sri299792458/robot-calibration-aprilcube-prototype/artifacts/g1_coupon_r2/renders/compact_coupons.png

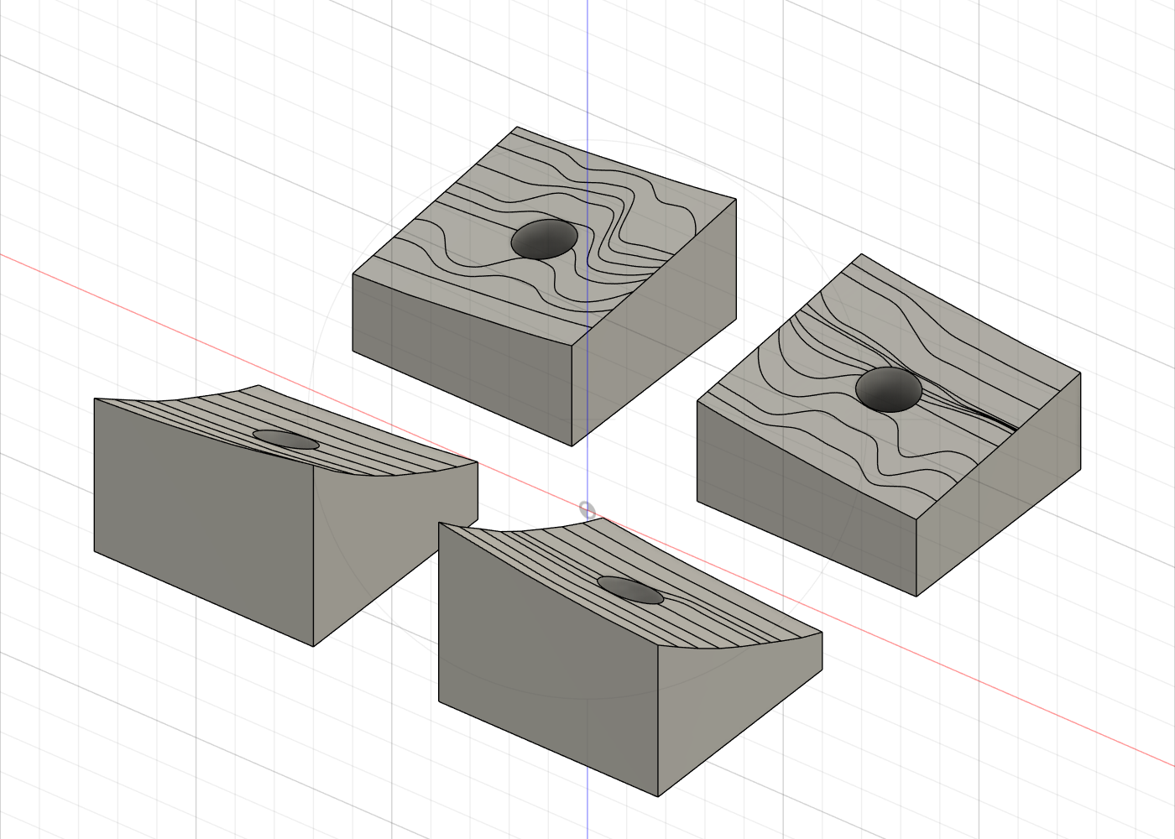
artifacts/g1_coupon_r2/renders/compact_coupons.png
