sri299792458/robot-calibration-aprilcube-prototype/artifacts/g1_coupon_r2/renders/identification_marks.png

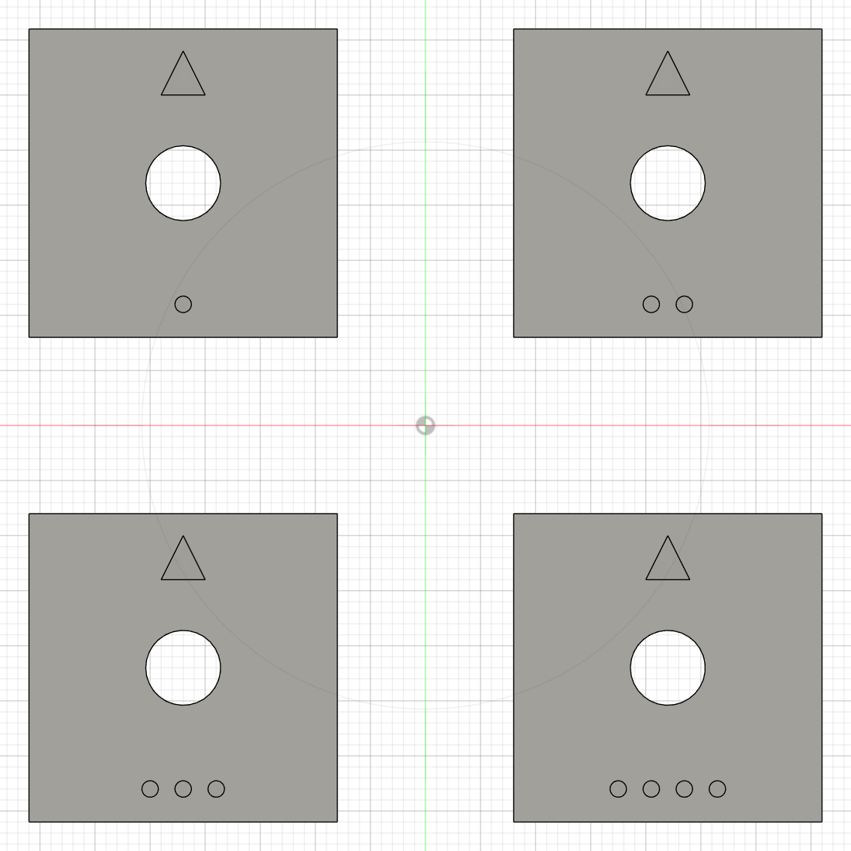
artifacts/g1_coupon_r2/renders/identification_marks.png
