sri299792458/robot-calibration-aprilcube-prototype/artifacts/g1_mount_v7/renders/board_connections.png

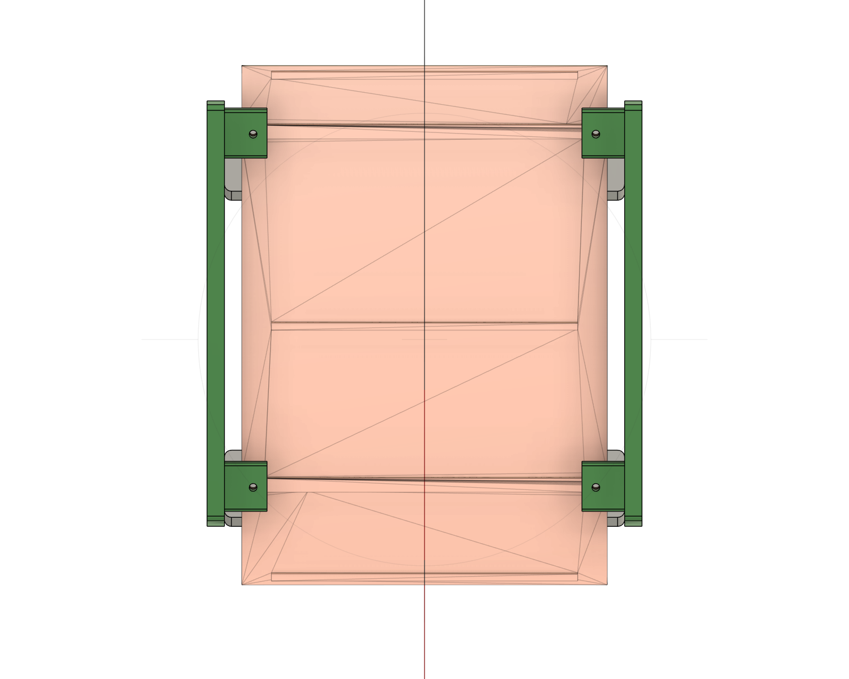
artifacts/g1_mount_v7/renders/board_connections.png
