sri299792458/robot-calibration-aprilcube-prototype/artifacts/g1_mount_v7/renders/m6_root_section.png

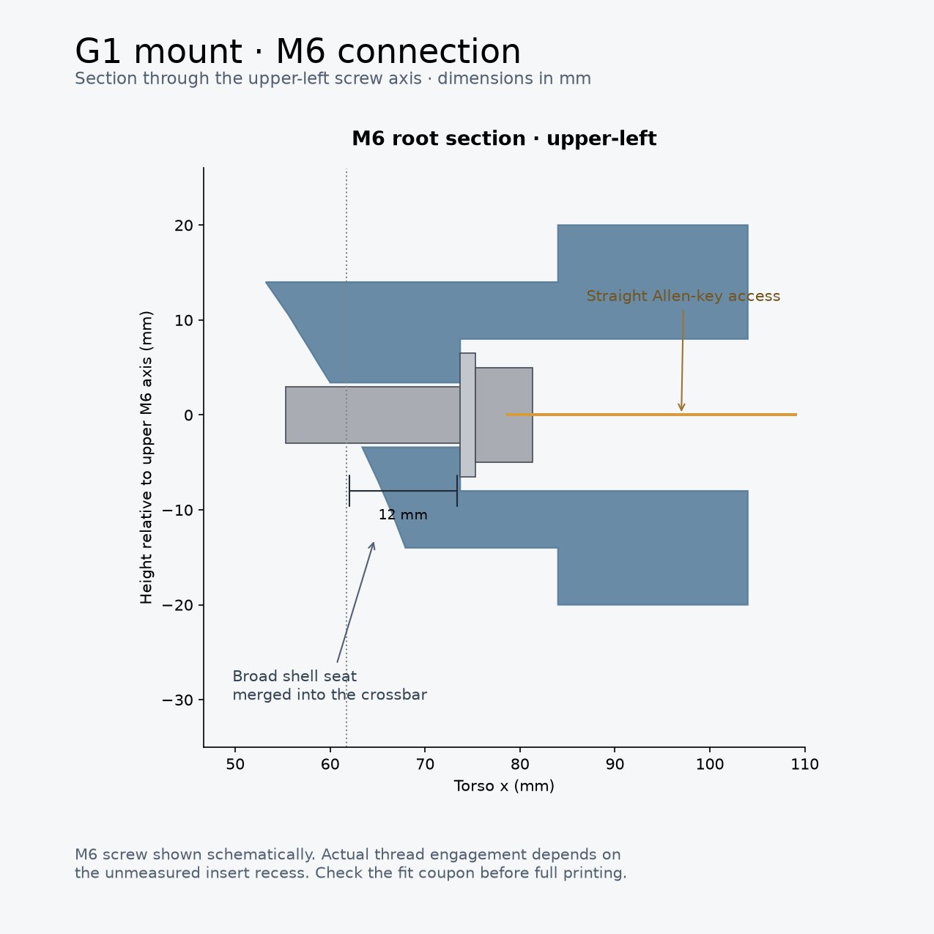
artifacts/g1_mount_v7/renders/m6_root_section.png
