sri299792458/robot-calibration-aprilcube-prototype/renders/dual_dex3_segmented_collision_envelopes.png

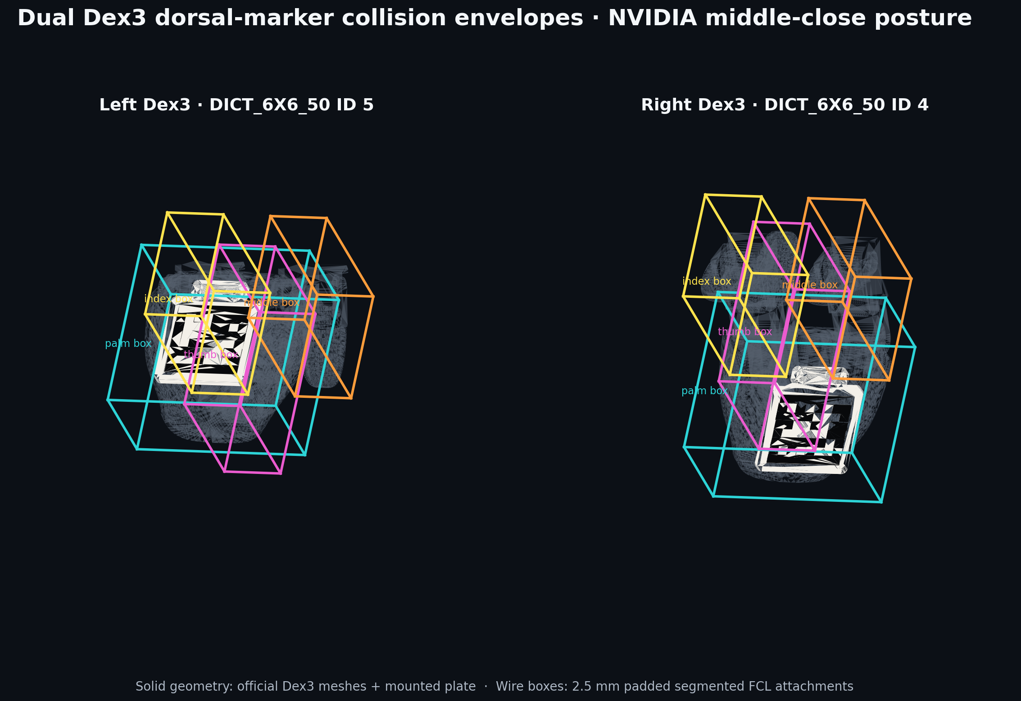
renders/dual_dex3_segmented_collision_envelopes.png
