sri299792458/robot-calibration-aprilcube-prototype/cad/dex3_dorsal_aruco_mount/carrier_white_pla.stl

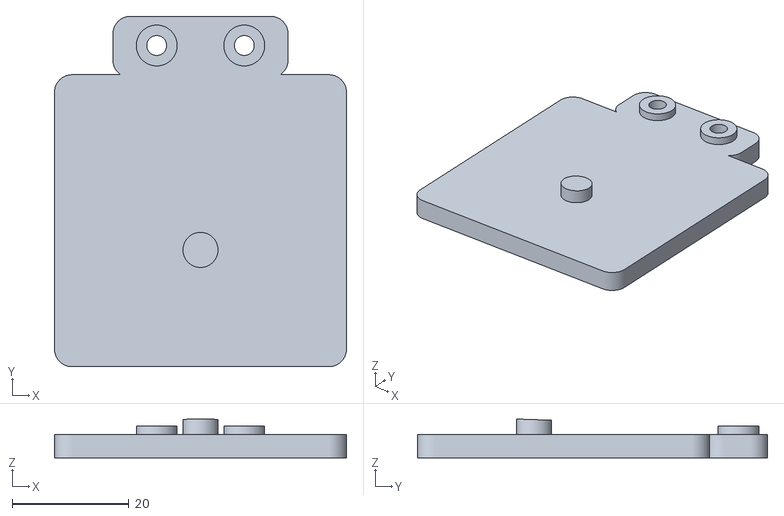
[picture p27: CAD file, 2026-09-21]
cad/dex3_dorsal_aruco_mount/carrier_white_pla.stl
50.0 x 60.0 x 6.67
