sri299792458/robot-calibration-aprilcube-prototype/cad/torso_charuco_fixture/carrier_multicolor_h2d.3mf

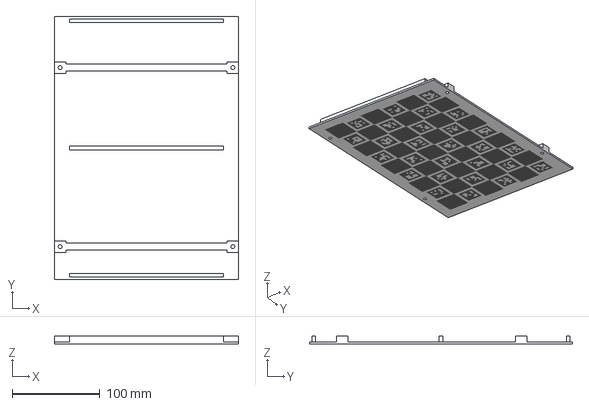
[picture p29: CAD file, 2026-09-21]
cad/torso_charuco_fixture/carrier_multicolor_h2d.3mf
210.0 x 300.0 x 9.40 mm
