sri299792458/robot-calibration-aprilcube-prototype/artifacts/g1_coupon_r2/original_reference/FIT_ONLY_lower_right_PRINT.stl

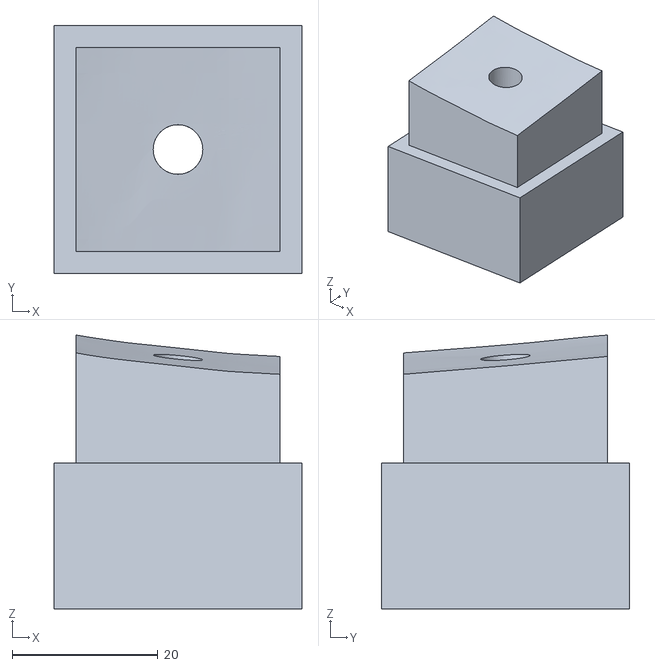
[picture p30: CAD file, 2026-09-21]
artifacts/g1_coupon_r2/original_reference/FIT_ONLY_lower_right_PRINT.stl
34.0 x 34.0 x 37.6
