sri299792458/robot-calibration-aprilcube-prototype/cad/dex3_dorsal_aruco_mount/aruco_black_pla.stl

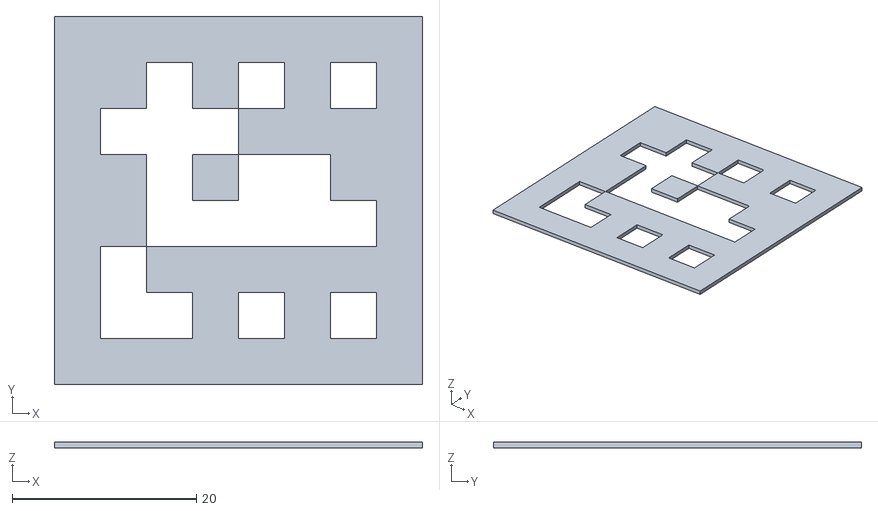
[picture p32: CAD file, 2026-09-21]
cad/dex3_dorsal_aruco_mount/aruco_black_pla.stl
40.0 x 40.0 x 0.6
