sri299792458/robot-calibration-aprilcube-prototype/artifacts/g1_mount_v7/renders/fusion_assembly.png

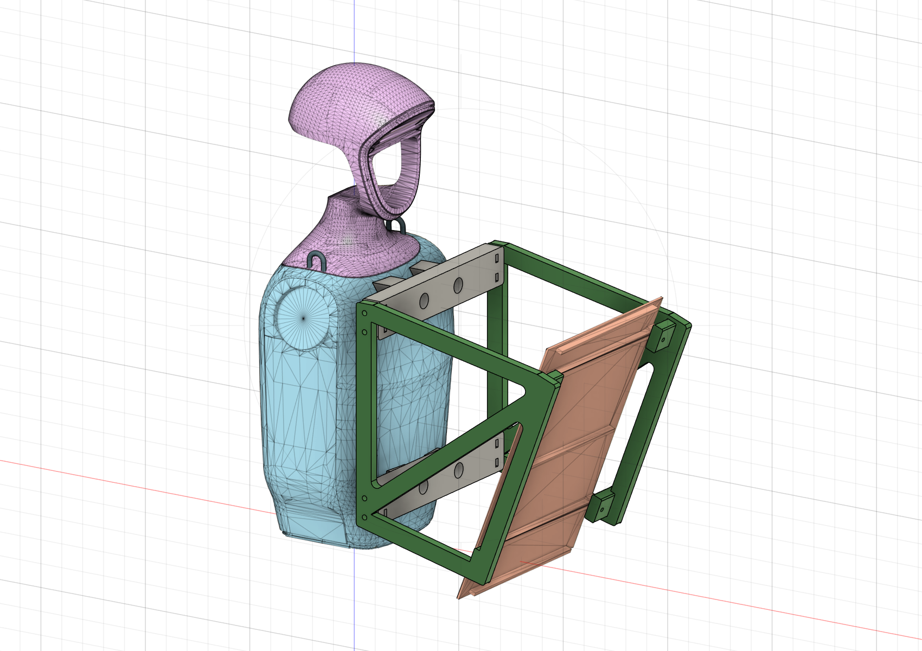
artifacts/g1_mount_v7/renders/fusion_assembly.png
