sri299792458/robot-calibration-aprilcube-prototype/artifacts/g1_mount_v7/renders/print_orientations.png

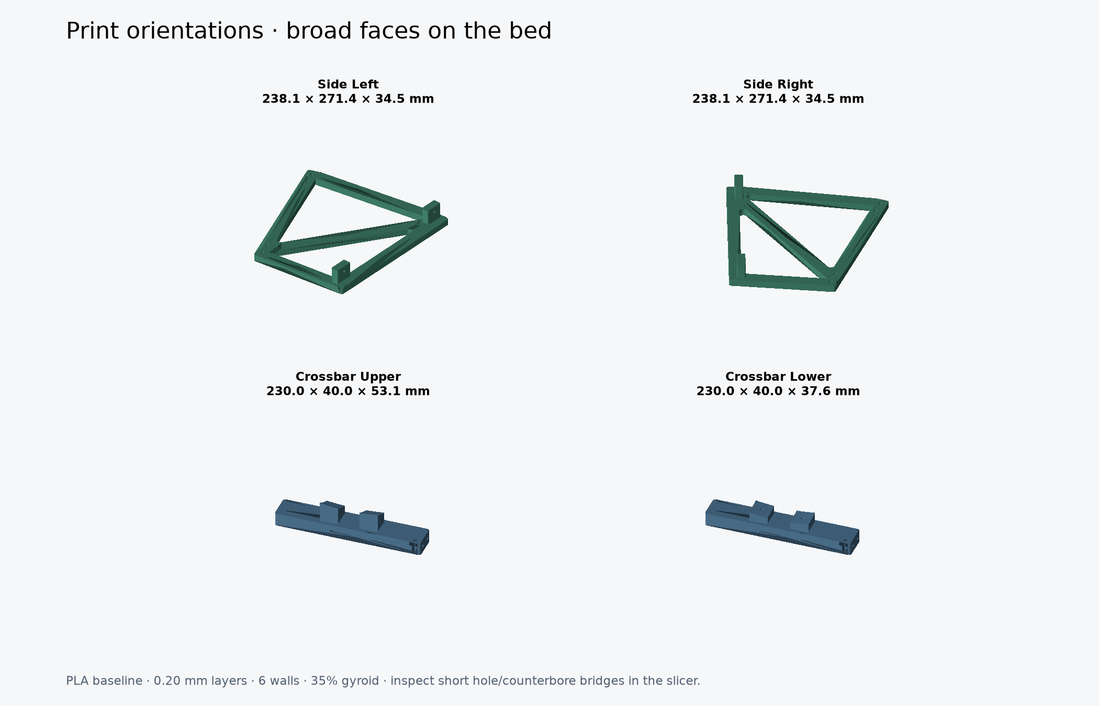
artifacts/g1_mount_v7/renders/print_orientations.png
