sri299792458/robot-calibration-aprilcube-prototype/src/g1_aprilcube_calibration/hardware_cli.py

"""Explicitly armed G1 commissioning and rectified-session collection commands."""

from __future__ import annotations

import argparse
import hashlib
import json
import os
import signal
import sys
import tempfile
import termios
import time
import tty
from collections.abc import Callable
from concurrent.futures import (
    ProcessPoolExecutor,
    as_completed,
)
from concurrent.futures import (
    TimeoutError as FuturesTimeoutError,
)
from dataclasses import replace
from itertools import pairwise
from multiprocessing import get_context
from pathlib import Path

import cv2
import numpy as np
import yaml
from scipy.spatial.transform import Rotation

from aprilcube import CorrespondenceDetector
from g1_aprilcube_calibration.activation_handoff import (
    ActivationHandoff,
    build_activation_handoff,
)
from g1_aprilcube_calibration.authored_collection import (
    AuthoredCollectionPlan,
    exposed_target_normal_from_hardware,
    modeled_hand_T_target_from_hardware,
    validate_exposed_camera_views,
    validate_hardware_target_profile,
    validate_modeled_hand_target_binding,
)
from g1_aprilcube_calibration.camera_models import RectifiedCameraInfo
from g1_aprilcube_calibration.capture_diagnostics import supported_vs_held_metrics
from g1_aprilcube_calibration.clock import SystemClock
from g1_aprilcube_calibration.collision import (
    CollisionConfig,
    FCLCollisionChecker,
)
from g1_aprilcube_calibration.config import QualityThresholds
from g1_aprilcube_calibration.dual_arm_clearance import (
    DUAL_CLEARANCE_POSE_ID,
    RIGHT_CLEARANCE_POSE_ID,
    DualArmClearanceExecutor,
    live_dex3_collision_config,
    plan_dual_arm_shoulder_clearance,
    validate_dex3_finger_sweep_at_state,
)
from g1_aprilcube_calibration.executor_driver import (
    ExecutorControlDriver,
    SynchronizedPoseExecutor,
)
from g1_aprilcube_calibration.executor_state_machine import (
    ExecutorConfig,
    ExecutorState,
    PoseExecutor,
)
from g1_aprilcube_calibration.gravity_compensation import (
    UNITREE_XR_GRAVITY_REFERENCE,
    G1PinocchioGravityFeedforward,
)
from g1_aprilcube_calibration.inverse_kinematics import IKConfig
from g1_aprilcube_calibration.joint_map import (
    G1_29_JOINT_NAMES,
    LEFT_ARM_INDICES,
    RIGHT_ARM_INDICES,
    arm_hand_link,
    arm_joint_names,
    validate_full_joint_vector,
)
from g1_aprilcube_calibration.live_capture import LiveBurstConfig, LiveBurstFrameSource
from g1_aprilcube_calibration.models import utc_now_iso
from g1_aprilcube_calibration.pc2_safety import (
    PC2DampingWatchdog,
    PC2SafetyConfig,
)
from g1_aprilcube_calibration.pose_recorder import (
    PoseRecorder,
    PoseRecordingRequest,
)
from g1_aprilcube_calibration.pose_schema import (
    HANDOFF_POSE_ID,
    PoseSet,
)
from g1_aprilcube_calibration.pose_store import PoseStore, TransientPoseStore
from g1_aprilcube_calibration.pose_validator import (
    DirectedEdgeResult,
    PathValidationConfig,
    PosePathValidator,
    ValidationReport,
)
from g1_aprilcube_calibration.preview import render_operator_preview
from g1_aprilcube_calibration.process_lock import CommandOwnerLock
from g1_aprilcube_calibration.quality import (
    CameraIntrinsics,
    PoseQualityEvaluator,
    QualityGrade,
    ViewSignature,
)
from g1_aprilcube_calibration.readiness import RecordingGateConfig, StateSampleBuffer
from g1_aprilcube_calibration.ros.camera_adapter import (
    ROSCameraSubscriber,
    ROSImageFrame,
)
from g1_aprilcube_calibration.session_runner import (
    ApprovedSessionOrchestrator,
    AuthoredCollectionOrchestrator,
    CaptureSessionRunner,
    SessionExecutionPlan,
)
from g1_aprilcube_calibration.session_runtime_log import SessionRuntimeLog
from g1_aprilcube_calibration.session_store import IsolatedSessionStore, SessionStore
from g1_aprilcube_calibration.table_accuracy import (
    CharucoBoardPoseDetector,
    CharucoBoardSpec,
    create_evaluation_document,
    create_plan_document,
    hand_target_from_board,
    load_plan_document,
    observe_burst,
    predicted_board_T_cube_from_model,
)
from g1_aprilcube_calibration.table_motion import (
    TABLE_ESCAPE_POSE_ID,
    TABLE_TARGET_POSE_ID,
    TablePlaneConfig,
    build_lifted_start_cube_target,
    build_table_motion_preflight,
    validate_table_plane_escape_path,
    validate_table_plane_path,
)
from g1_aprilcube_calibration.teaching_controller import (
    TeachingArmController,
    TeachingConfig,
    TeachingState,
)
from g1_aprilcube_calibration.teaching_driver import (
    SynchronizedTeachingController,
    TeachingControlDriver,
)
from g1_aprilcube_calibration.timestamp_pairing import PairingConfig
from g1_aprilcube_calibration.transforms import validate_transform
from g1_aprilcube_calibration.transports.base import ArmCommand
from g1_aprilcube_calibration.transports.unitree_arm_sdk import (
    UnitreeArmSDKTransport,
    UnitreeLowStateObserver,
    UnitreeTransportConfig,
)
from g1_aprilcube_calibration.transports.unitree_debug_lowcmd import (
    UnitreeDebugLowCmdConfig,
    UnitreeDebugLowCmdTransport,
)
from g1_aprilcube_calibration.transports.unitree_dex3 import (
    DEX3_CALIBRATION_POSTURE_SOURCE,
    DEX3_MOTOR_JOINT_SUFFIXES,
    Dex3ControlConfig,
    UnitreeDex3PostureController,
    UnitreeDex3StateObserver,
    dex3_motor_joint_name,
)
from g1_aprilcube_calibration.urdf_model import URDFModel

WRITE_ACK = "I UNDERSTAND THIS WRITES RT/ARM_SDK"
DAMP_ACK = "DAMP THE LOAD-BEARING-HARNESSED G1 NOW"
MOTION_ACK = (
    "I CONFIRM THE G1 IS SECURED BY THE LOAD-BEARING HARNESS AND THE WORKSPACE IS CLEAR"
)
LIVE_TEACHING_YELLOW_REASON = "operator accepted yellow warning in live teaching UI"
_MAX_RUNTIME_VALIDATION_WORKERS = 8
_MINIMUM_PARALLEL_VALIDATION_EDGES = 8
_runtime_validation_worker: tuple[PosePathValidator, object, np.ndarray] | None = None
REPLAY_YELLOW_REASON = "yellow visual warning accepted by replay default"


def add_hardware_subparsers(
    subparsers: argparse._SubParsersAction,
    *,
    workspace_root: Path,
    default_target: Path,
    default_quality: Path,
) -> None:
    default_hardware = workspace_root / "config" / "hardware_dex3_aruco.yaml"
    default_collision = workspace_root / "config" / "collision_pairs_dex3_aruco.yaml"
    default_lock = Path("/tmp/g1-aprilcube-calibration-command.lock")

    table_images = subparsers.add_parser(
        "capture-table-images",
        help="save a camera-only lossless burst for the tabletop accuracy test",
    )
    _add_network_arguments(table_images)
    _add_camera_arguments(table_images)
    table_images.add_argument("--output-directory", type=Path, required=True)
    table_images.add_argument("--frame-count", type=int, default=7)
    table_images.add_argument("--camera-timeout-s", type=float, default=10.0)
    table_images.add_argument("--maximum-duration-s", type=float, default=2.0)
    table_images.set_defaults(handler=run_capture_table_images)

    table_execute = subparsers.add_parser(
        "execute-table-accuracy",
        help=(
            "solve a supported-start escape and table target, capture, reverse "
            "to the supported start, restore seated control, and score accuracy"
        ),
    )
    _add_network_arguments(table_execute)
    _add_motion_safety_arguments(table_execute)
    _add_camera_arguments(table_execute)
    table_execute.add_argument("--plan", type=Path, required=True)
    table_execute.add_argument("--output-directory", type=Path, required=True)
    table_execute.add_argument("--hardware-config", type=Path, default=default_hardware)
    table_execute.add_argument(
        "--collision-config", type=Path, default=default_collision
    )
    table_execute.add_argument("--frame-count", type=int, default=7)
    table_execute.add_argument("--camera-timeout-s", type=float, default=10.0)
    table_execute.add_argument("--maximum-burst-duration-s", type=float, default=2.0)
    table_execute.add_argument("--ik-restarts", type=int, default=24)
    table_execute.add_argument("--minimum-board-clearance-mm", type=float, default=10.0)
    table_execute.add_argument("--maximum-board-shift-mm", type=float, default=5.0)
    table_execute.add_argument("--maximum-board-shift-deg", type=float, default=1.0)
    table_execute.add_argument(
        "--confirm", required=True, help=f"must equal: {MOTION_ACK}"
    )
    table_execute.add_argument("--lock-file", type=Path, default=default_lock)
    table_execute.set_defaults(handler=run_execute_table_accuracy)

    zero = subparsers.add_parser(
        "commission-weight-zero",
        help="publish one measured arm target with blend weight zero",
    )
    _add_network_arguments(zero)
    zero.add_argument("--confirm", required=True, help=f"must equal: {WRITE_ACK}")
    zero.add_argument("--timeout-s", type=float, default=5.0)
    zero.add_argument("--lock-file", type=Path, default=default_lock)
    zero.set_defaults(handler=run_commission_weight_zero)

    damping = subparsers.add_parser(
        "commission-damping",
        help="physically verify the PC2 heartbeat watchdog and G1 Damp RPC",
    )
    _add_network_arguments(damping)
    _add_motion_safety_arguments(damping)
    damping.add_argument("--hardware-config", type=Path, default=default_hardware)
    damping.add_argument(
        "--trigger",
        choices=("heartbeat-timeout", "explicit"),
        default="heartbeat-timeout",
    )
    damping.add_argument("--confirm", required=True, help=f"must equal: {DAMP_ACK}")
    damping.set_defaults(handler=run_commission_damping)

    dex3_posture = subparsers.add_parser(
        "commission-dex3-middle-close",
        help=(
            "derive and execute a live collision-validated shoulder-clearance "
            "route, verify NVIDIA middle-close, restore the original fingers "
            "and shoulders, and send terminal Dex3 timeout"
        ),
    )
    _add_network_arguments(dex3_posture)
    _add_motion_safety_arguments(dex3_posture)
    dex3_posture.add_argument("--hardware-config", type=Path, default=default_hardware)
    dex3_posture.add_argument(
        "--collision-config", type=Path, default=default_collision
    )
    dex3_posture.add_argument("--duration-s", type=float, default=2.0)
    dex3_posture.add_argument(
        "--confirm", required=True, help=f"must equal: {MOTION_ACK}"
    )
    dex3_posture.add_argument("--lock-file", type=Path, default=default_lock)
    dex3_posture.set_defaults(handler=run_commission_dex3_middle_close)

    seated_debug_hold = subparsers.add_parser(
        "commission-seated-debug-hold",
        help=(
            "commission zero-displacement seated debug lowcmd takeover and "
            "verified normal FSM 0 -> 1 -> 3 restoration"
        ),
    )
    _add_network_arguments(seated_debug_hold)
    _add_motion_safety_arguments(seated_debug_hold)
    seated_debug_hold.add_argument(
        "--hardware-config", type=Path, default=default_hardware
    )
    seated_debug_hold.add_argument(
        "--collision-config", type=Path, default=default_collision
    )
    seated_debug_hold.add_argument("--duration-s", type=float, default=2.0)
    seated_debug_hold.add_argument(
        "--trigger",
        choices=("restore-seated", "heartbeat-zero-torque"),
        default="restore-seated",
        help=(
            "restore AI through verified FSM 0 -> 1 -> 3 or "
            "deliberately stop command/heartbeat publication and verify PC2 "
            "independently restores AI in zero-torque FSM 0"
        ),
    )
    seated_debug_hold.add_argument(
        "--confirm", required=True, help=f"must equal: {MOTION_ACK}"
    )
    seated_debug_hold.add_argument("--lock-file", type=Path, default=default_lock)
    seated_debug_hold.set_defaults(handler=run_commission_seated_debug_hold)

    teach = subparsers.add_parser(
        "teach-poses",
        help=(
            "continuously guide the arm through arm_sdk, freeze measured poses, "
            "and record paired supported/held calibration bursts"
        ),
    )
    _add_network_arguments(teach)
    _add_motion_safety_arguments(teach)
    teach.add_argument("--session-directory", type=Path, required=True)
    teach.add_argument("--session-id", required=True)
    _add_camera_arguments(teach)
    teach.add_argument("--hardware-config", type=Path, default=default_hardware)
    teach.add_argument("--collision-config", type=Path, default=default_collision)
    teach.add_argument("--target-config", type=Path, default=default_target)
    teach.add_argument("--quality-config", type=Path, default=default_quality)
    teach.add_argument("--camera-timeout-s", type=float, default=10.0)
    teach.add_argument("--guide-camera-timeout-s", type=float, default=1.0)
    teach.add_argument("--burst-timeout-s", type=float, default=15.0)
    teach.add_argument("--group", default="calibration")
    teach.add_argument("--first-pose-id", default="pose_001")
    teach.add_argument("--preview-directory", type=Path)
    teach.add_argument(
        "--yellow-override-reason",
        help=(
            "optional custom note for yellow views; without it, SPACE accepts yellow "
            "and stores the standard live-operator warning"
        ),
    )
    teach.add_argument("--confirm", required=True, help=f"must equal: {MOTION_ACK}")
    teach.add_argument("--lock-file", type=Path, default=default_lock)
    teach.set_defaults(handler=run_teach_poses)

    hold = subparsers.add_parser(
        "commission-hold",
        help="derive a stationary handoff, then acquire/release arm_sdk there",
    )
    _add_network_arguments(hold)
    _add_motion_safety_arguments(hold)
    hold.add_argument("--pose-set", type=Path, required=True)
    hold.add_argument("--hardware-config", type=Path, default=default_hardware)
    hold.add_argument("--collision-config", type=Path, default=default_collision)
    hold.add_argument("--duration-s", type=float, default=2.0)
    hold.add_argument("--confirm", required=True, help=f"must equal: {MOTION_ACK}")
    hold.add_argument("--lock-file", type=Path, default=default_lock)
    hold.set_defaults(handler=run_commission_hold)

    pose = subparsers.add_parser(
        "commission-pose",
        help="validate a live handoff, visit one pose, return, and release",
    )
    _add_network_arguments(pose)
    _add_motion_safety_arguments(pose)
    pose.add_argument("--pose-set", type=Path, required=True)
    pose.add_argument("--validation-report", type=Path, required=True)
    pose.add_argument("--target-pose", required=True)
    pose.add_argument("--hardware-config", type=Path, default=default_hardware)
    pose.add_argument("--collision-config", type=Path, default=default_collision)
    pose.add_argument("--confirm", required=True, help=f"must equal: {MOTION_ACK}")
    pose.add_argument("--lock-file", type=Path, default=default_lock)
    pose.set_defaults(handler=run_commission_pose)

    collect = subparsers.add_parser(
        "collect-session",
        help="execute a passed pose plan and write an immutable rectified session",
    )
    _add_network_arguments(collect)
    _add_motion_safety_arguments(collect)
    collect.add_argument("--pose-set", type=Path, required=True)
    collect.add_argument("--validation-report", type=Path, required=True)
    collect.add_argument("--plan-yaml", type=Path, required=True)
    collect.add_argument("--session-directory", type=Path, required=True)
    collect.add_argument("--session-id", required=True)
    _add_camera_arguments(collect)
    collect.add_argument("--hardware-config", type=Path, default=default_hardware)
    collect.add_argument("--collision-config", type=Path, default=default_collision)
    collect.add_argument("--target-config", type=Path, default=default_target)
    collect.add_argument("--quality-config", type=Path, default=default_quality)
    collect.add_argument("--camera-timeout-s", type=float, default=10.0)
    collect.add_argument("--burst-timeout-s", type=float, default=3.0)
    collect.add_argument(
        "--head-witness-ack",
        action="store_true",
        required=True,
        help="confirm the current fixed camera/head witness mark before collection",
    )
    collect.add_argument("--auto-confirm-transitions", action="store_true")
    collect.add_argument("--no-window", action="store_true")
    collect.add_argument("--confirm", required=True, help=f"must equal: {MOTION_ACK}")
    collect.add_argument("--lock-file", type=Path, default=default_lock)
    collect.set_defaults(handler=run_collect_session)

    collect_auto = subparsers.add_parser(
        "collect-auto",
        help=(
            "execute an authored standing calibration route, automatically "
            "capture valid views, and skip red/invisible targets"
        ),
    )
    _add_network_arguments(collect_auto)
    _add_motion_safety_arguments(collect_auto)
    collect_auto.add_argument("--plan", type=Path, required=True)
    collect_auto.add_argument("--session-directory", type=Path, required=True)
    collect_auto.add_argument("--session-id", required=True)
    _add_camera_arguments(collect_auto)
    collect_auto.add_argument("--hardware-config", type=Path, default=default_hardware)
    collect_auto.add_argument(
        "--collision-config", type=Path, default=default_collision
    )
    collect_auto.add_argument("--target-config", type=Path, default=default_target)
    collect_auto.add_argument("--quality-config", type=Path, default=default_quality)
    collect_auto.add_argument("--camera-timeout-s", type=float, default=10.0)
    collect_auto.add_argument("--burst-timeout-s", type=float, default=3.0)
    collect_auto.add_argument("--no-window", action="store_true")
    collect_auto.add_argument(
        "--confirm", required=True, help=f"must equal: {MOTION_ACK}"
    )
    collect_auto.add_argument("--lock-file", type=Path, default=default_lock)
    collect_auto.set_defaults(handler=run_collect_auto)


def _add_network_arguments(parser: argparse.ArgumentParser) -> None:
    parser.add_argument("--network-interface", required=True)
    parser.add_argument("--domain-id", type=int, default=0)


def _add_motion_safety_arguments(parser: argparse.ArgumentParser) -> None:
    parser.add_argument(
        "--pc2-host",
        default=os.environ.get("G1_PC2_HOST", "unitree@192.168.123.164"),
    )
    parser.add_argument(
        "--pc2-ssh-identity",
        type=Path,
        default=Path(
            os.environ.get(
                "G1_PC2_SSH_IDENTITY",
                str(Path.home() / ".ssh" / "g1_pc2_ed25519"),
            )
        ),
    )


def _add_camera_arguments(parser: argparse.ArgumentParser) -> None:
    parser.add_argument("--image-topic", required=True)
    parser.add_argument("--camera-info-topic", required=True)
    parser.add_argument("--camera-name", required=True)
    parser.add_argument("--camera-serial", required=True)
    parser.add_argument(
        "--ros-camera-reliability",
        choices=("reliable", "best-effort"),
        default="reliable",
        help=(
            "ROS Image/CameraInfo subscription reliability; calibration defaults "
            "to reliable"
        ),
    )


def run_capture_table_images(args: argparse.Namespace) -> int:
    """Capture rectified images without constructing any robot transport."""
    if args.frame_count < 3:
        raise ValueError("--frame-count must be at least 3")
    if args.maximum_duration_s <= 0:
        raise ValueError("--maximum-duration-s must be positive")
    output = args.output_directory.resolve()
    if output.exists():
        raise FileExistsError(f"table image burst already exists: {output}")
    try:
        import rclpy
    except ImportError as error:
        raise RuntimeError(
            "rclpy is unavailable; source the ROS environment"
        ) from error

    rclpy.init(args=None)
    node = rclpy.create_node("g1_table_accuracy_image_capture")
    camera = None
    try:
        camera = ROSCameraSubscriber(
            node,
            image_topic=args.image_topic,
            camera_info_topic=args.camera_info_topic,
            camera_name=args.camera_name,
            serial_number=args.camera_serial,
            reliability=args.ros_camera_reliability,
            maximum_frames=max(30, args.frame_count * 2),
        )
        _wait_for_camera(rclpy, node, camera, args.camera_timeout_s)
        frames = _collect_new_camera_frames(
            rclpy,
            node,
            camera,
            frame_count=args.frame_count,
            timeout_s=args.camera_timeout_s,
            maximum_duration_s=args.maximum_duration_s,
        )
    finally:
        if camera is not None:
            camera.close()
        node.destroy_node()
        _shutdown_rclpy_once(rclpy)

    manifest = _write_table_image_burst(output, frames)
    print(json.dumps({**manifest, "output": str(output)}, indent=2, sort_keys=True))
    return 0


def run_execute_table_accuracy(args: argparse.Namespace) -> int:
    """Acquire while seated, run one table trial, and release at the start pose."""

    _require_ack(args.confirm, MOTION_ACK)
    _require_dex3_posture_commissioned(args.hardware_config)
    _validate_table_execution_arguments(args)
    with args.hardware_config.open(encoding="utf-8") as stream:
        table_hardware = yaml.safe_load(stream)
    table_control = table_hardware["control"]
    if table_control.get("seated_table_control") != "debug_lowcmd":
        raise RuntimeError(
            "seated tabletop execution requires control.seated_table_control="
            "debug_lowcmd"
        )
    if table_control.get("seated_debug_lowcmd_commissioned") is not True:
        raise RuntimeError(
            "seated tabletop execution is blocked before command creation: the "
            "debug rt/lowcmd takeover, normal FSM 0 -> 1 -> 3 restoration, and "
            "heartbeat-loss AI restoration to zero-torque FSM 0 have not been "
            "commissioned on this robot"
        )
    if table_control.get("seated_gravity_feedforward_commissioned") is not True:
        raise RuntimeError(
            "seated tabletop execution is blocked before command creation: "
            "Unitree-style Pinocchio gravity feedforward has not passed its "
            "zero-displacement seated debug commissioning run"
        )
    output = args.output_directory.resolve()
    if output.exists():
        raise FileExistsError(f"table-accuracy run already exists: {output}")

    input_plan = load_plan_document(args.plan)
    plan = input_plan
    model = URDFModel(_configured_urdf(args.hardware_config))
    _validate_table_plan_artifacts(plan, model=model)
    empty_pose_set = PoseSet(
        robot_model=model.name,
        mode_machine=5,
        urdf_sha256=model.sha256,
        calibration_arm=plan["calibration_arm"],
    )
    hardware_bytes = args.hardware_config.read_bytes()
    _validate_hardware_preflight(
        hardware_bytes,
        empty_pose_set,
        require_poses=False,
    )
    collision_bytes = args.collision_config.read_bytes()
    collision = _validate_collision_preflight(args.collision_config)
    if args.collision_config.read_bytes() != collision_bytes:
        raise RuntimeError("collision configuration changed during preflight")
    recording, _, executor_config, rate_hz = _runtime_configs(args.hardware_config)
    camera_info = RectifiedCameraInfo.from_dict(plan["camera_info"])
    board_spec = CharucoBoardSpec.from_dict(plan["board_spec"])
    board_detector = CharucoBoardPoseDetector(board_spec)
    table_plane_config = TablePlaneConfig(
        board_width_m=board_spec.width_mm / 1000.0,
        board_height_m=board_spec.height_mm / 1000.0,
        table_margin_m=0.2,
        minimum_clearance_m=args.minimum_board_clearance_mm / 1000.0,
    )
    hand_cube_path = Path(plan["sources"]["hand_cube_config_path"])
    hand_cube_detector = CorrespondenceDetector(hand_cube_path)
    torso_T_camera = validate_transform(
        np.asarray(plan["calibration"]["torso_T_camera"], dtype=np.float64)
    )
    hand_T_cube = validate_transform(
        np.asarray(plan["calibration"]["hand_T_cube"], dtype=np.float64)
    )
    try:
        import rclpy
    except ImportError as error:
        raise RuntimeError(
            "rclpy is unavailable; source the ROS environment"
        ) from error

    rclpy.init(args=None)
    node = rclpy.create_node("g1_table_accuracy_executor")
    camera = None
    observer = None
    dex3_observer = None
    dex3_controller = None
    dex3_posture_evidence = None
    transport = None
    watchdog = None
    synchronized = None
    driver = None
    preflight_frames: tuple[ROSImageFrame, ...] = ()
    loaded_planning_frames: tuple[ROSImageFrame, ...] = ()
    verification_frames: tuple[ROSImageFrame, ...] = ()
    loaded_planning_rejections: tuple[str, ...] = ()
    verification_rejections: tuple[str, ...] = ()
    achieved_frames: tuple[ROSImageFrame, ...] = ()
    initial_observation = None
    loaded_planning_observation = None
    verification_observation = None
    execution_plan = None
    motion_preflight = None
    final_report = None
    final_escape_clearance = None
    final_elevated_route_clearance = None
    final_activation = None
    board_shift = None
    initial_cube_shift = None
    takeover_board_shift = None
    takeover_cube_shift = None
    approval_cube_shift = None
    escape_outbound_duration_s = None
    supported_return_timeout_s = None
    capture_failure = None
    attained_escape_outbound = None
    attained_target_before_capture = None
    attained_target_after_capture = None
    attained_escape_return = None
    attained_supported_return = None
    target_capture_position_spread_rad = None
    primary_error: BaseException | None = None
    command_lock = CommandOwnerLock(args.lock_file)
    command_lock.acquire()
    try:
        camera = ROSCameraSubscriber(
            node,
            image_topic=args.image_topic,
            camera_info_topic=args.camera_info_topic,
            camera_name=args.camera_name,
            serial_number=args.camera_serial,
            reliability=args.ros_camera_reliability,
            maximum_frames=max(30, args.frame_count * 3),
        )
        states = StateSampleBuffer()
        observer = UnitreeLowStateObserver(
            _transport_config(args),
            on_sample=states.add,
        )
        _wait_for_state(observer, 5.0)
        dex3_observer = UnitreeDex3StateObserver(
            _dex3_control_config(args),
            initialize_factory=False,
        )
        _wait_for_dex3_state(dex3_observer, 5.0)
        _wait_for_camera(rclpy, node, camera, args.camera_timeout_s)
        live_camera_info = camera.frames.latest.camera_info
        if live_camera_info.profile_sha256 != camera_info.profile_sha256:
            raise ValueError("live camera profile differs from the table-accuracy plan")

        print(
            "PRECHECK — keep the robot and fixed table board still; "
            "collecting a live board/cube burst"
        )
        preflight_frames = _collect_new_camera_frames(
            rclpy,
            node,
            camera,
            frame_count=args.frame_count,
            timeout_s=args.camera_timeout_s,
            maximum_duration_s=args.maximum_burst_duration_s,
        )
        initial_observation = _observe_table_frames(
            preflight_frames,
            camera_info=camera_info,
            hand_cube_detector=hand_cube_detector,
            board_detector=board_detector,
        )
        initial_camera_T_board = _observation_transform(
            initial_observation,
            "camera_T_board",
        )
        initial_board_T_cube = _observation_transform(
            initial_observation,
            "board_T_hand_cube",
        )
        planned_initial_board_T_cube = validate_transform(
            np.asarray(
                plan["target"]["initial_board_T_hand_cube"],
                dtype=np.float64,
            )
        )
        initial_cube_shift = _transform_delta(
            planned_initial_board_T_cube,
            initial_board_T_cube,
        )
        if initial_cube_shift["translation_mm"] > args.maximum_board_shift_mm:
            raise ValueError(
                "live supported cube differs from the planned initial cube by "
                f"{initial_cube_shift['translation_mm']:.3f}mm; limit is "
                f"{args.maximum_board_shift_mm:.3f}mm. No robot command was sent"
            )
        if initial_cube_shift["rotation_deg"] > args.maximum_board_shift_deg:
            raise ValueError(
                "live supported cube orientation differs from the planned initial "
                f"orientation by {initial_cube_shift['rotation_deg']:.3f}deg; "
                f"limit is {args.maximum_board_shift_deg:.3f}deg. No robot command "
                "was sent"
            )
        activation = _wait_for_activation_handoff(
            observer,
            states,
            empty_pose_set,
            recording,
        )
        print(
            "READ-ONLY SETUP PASSED — camera, board, cube, artifacts, and "
            "stationary arms are valid; no IK/FCL route has been frozen and no "
            "robot command has been published"
        )
        _wait_for_space(
            "START — confirm the G1 is seated; leave both forearms supported "
            "and stationary with every finger clear to curl; clear the complete "
            "lift/target/return sweep. "
            "Press SPACE once to acquire, settle under load, observe and plan "
            "from that loaded state, execute one open-loop trial, return, and "
            "restore seated control through FSM 0 -> 1 -> 3: "
        )

        if args.hardware_config.read_bytes() != hardware_bytes:
            raise RuntimeError(
                "hardware configuration changed during preflight; no robot command was sent"
            )
        if args.collision_config.read_bytes() != collision_bytes:
            raise RuntimeError(
                "collision configuration changed during preflight; no robot command was sent"
            )
        live_urdf_sha256 = hashlib.sha256(
            _configured_urdf(args.hardware_config).read_bytes()
        ).hexdigest()
        if live_urdf_sha256 != model.sha256:
            raise RuntimeError(
                "URDF changed during preflight; no robot command was sent"
            )
        activation = _wait_for_activation_handoff(
            observer,
            states,
            empty_pose_set,
            recording,
        )
        gravity_feedforward = _gravity_feedforward(args.hardware_config)
        gravity_feedforward.seed_reference(activation.reference_state.position)
        takeover_q14 = np.concatenate(
            (
                activation.reference_state.left_q,
                activation.reference_state.right_q,
            )
        )
        takeover_gravity_tau = gravity_feedforward.torque_for(takeover_q14)
        _print_gravity_preflight(gravity_feedforward, takeover_gravity_tau)
        print(
            "TAKEOVER CHECK PASSED — PC2 will verify seated FSM 3 and the laptop "
            "will acquire complete 29-joint debug lowcmd control at the exact "
            "measured state; IK/FCL planning will happen only after loaded settling"
        )

        watchdog = _pc2_damping_watchdog(
            args,
            args.hardware_config,
            require_regular=False,
            required_initial_fsm_id=_seated_fsm_id(args.hardware_config),
            restore_motion_service_before_loco=True,
        )
        transport = UnitreeDebugLowCmdTransport(
            _transport_config(args),
            _debug_lowcmd_config(args.hardware_config),
            observer=observer,
            ownership_keepalive=watchdog.pulse,
        )
        observer = None
        _wait_for_state(transport, 5.0)
        dex3_controller = UnitreeDex3PostureController(
            _dex3_control_config(args),
            observer=dex3_observer,
        )
        dex3_observer = None
        table_executor_config = replace(
            executor_config,
            require_motion_endpoint_tolerance=False,
        )
        raw_executor = PoseExecutor(
            transport=transport,
            clock=SystemClock(),
            pose_set=empty_pose_set,
            handoff_q=activation.handoff_q,
            hold_q=activation.hold_q,
            approved_validation_report_sha256=input_plan["content_sha256"],
            config=table_executor_config,
            gravity_feedforward=gravity_feedforward,
        )
        synchronized = SynchronizedPoseExecutor(raw_executor)
        driver = ExecutorControlDriver(
            synchronized,
            rate_hz=rate_hz,
            safety_heartbeat=_dex3_safety_heartbeat(
                watchdog,
                dex3_controller,
            ),
        )
        # Complete every non-commanding DDS and executor setup before arming
        # PC2's 0.5 s lease. The next actions start the control thread and
        # execute the guarded ReleaseMode/first-lowcmd transition.
        watchdog.start()
        dex3_posture_evidence = dex3_controller.acquire_posture(
            safety_heartbeat=watchdog.pulse,
        )
        print(
            "DEX3 CALIBRATION POSTURE ACQUIRED — both hands reached NVIDIA's "
            "middle-close target; posture commands remain active throughout "
            "seated body control"
        )
        driver.start()
        synchronized.acquire(operator_confirmed=True)
        _wait_for_driven_state(
            synchronized,
            driver,
            ExecutorState.READY,
            rclpy=rclpy,
            node=node,
            timeout_s=executor_config.acquisition_ramp_s + 5.0,
        )
        print(
            "CONTROL ACQUIRED — holding the measured state under full gravity "
            "feedforward; collecting the loaded board/cube observation now. "
            "No changing arm target has been issued"
        )
        (
            loaded_planning_frames,
            loaded_planning_observation,
            loaded_planning_rejections,
        ) = _capture_controlled_table_observation(
            synchronized=synchronized,
            driver=driver,
            collect=lambda: _collect_new_camera_frames(
                rclpy,
                node,
                camera,
                frame_count=args.frame_count,
                timeout_s=args.camera_timeout_s,
                maximum_duration_s=args.maximum_burst_duration_s,
                control_check=driver.check,
            ),
            observe=lambda frames: _observe_table_frames(
                frames,
                camera_info=camera_info,
                hand_cube_detector=hand_cube_detector,
                board_detector=board_detector,
            ),
            label="post-takeover loaded-state planning",
        )
        loaded_camera_T_board = _observation_transform(
            loaded_planning_observation,
            "camera_T_board",
        )
        loaded_board_T_cube = _observation_transform(
            loaded_planning_observation,
            "board_T_hand_cube",
        )
        takeover_board_shift = _transform_delta(
            initial_camera_T_board,
            loaded_camera_T_board,
        )
        takeover_cube_shift = _transform_delta(
            initial_board_T_cube,
            loaded_board_T_cube,
        )
        loaded_activation = _wait_for_activation_handoff(
            synchronized,
            states,
            empty_pose_set,
            recording,
        )
        print(
            "POST-TAKEOVER REPLAN — the controller is holding the loaded handoff "
            "while IK and FCL run; no changing arm target has been issued"
        )
        target_xy = tuple(float(value) for value in input_plan["target"]["board_xy_mm"])
        execution_plan = create_plan_document(
            dataset_path=input_plan["sources"]["dataset_path"],
            result_path=input_plan["sources"]["result_path"],
            hand_cube_config_path=input_plan["sources"]["hand_cube_config_path"],
            planning_burst=loaded_planning_observation,
            board_spec=board_spec,
            lift_mm=float(input_plan["target"]["lift_above_initial_cube_mm"]),
            board_xy_mm=(target_xy[0], target_xy[1]),
        )
        _validate_table_plan_artifacts(execution_plan, model=model)
        plan = execution_plan
        desired_board_T_cube = validate_transform(
            np.asarray(
                plan["target"]["desired_board_T_hand_cube"],
                dtype=np.float64,
            )
        )
        desired_board_T_escape = build_lifted_start_cube_target(
            current_board_T_cube=loaded_board_T_cube,
            desired_board_T_cube=desired_board_T_cube,
        )
        desired_torso_T_escape = hand_target_from_board(
            torso_T_camera=torso_T_camera,
            hand_T_cube=hand_T_cube,
            camera_T_board=loaded_camera_T_board,
            desired_board_T_cube=desired_board_T_escape,
        )
        desired_torso_T_hand = hand_target_from_board(
            torso_T_camera=torso_T_camera,
            hand_T_cube=hand_T_cube,
            camera_T_board=loaded_camera_T_board,
            desired_board_T_cube=desired_board_T_cube,
        )
        motion_preflight = _run_isolated_control_work(
            label="post-takeover IK/FCL planning",
            worker=_build_table_motion_preflight_worker,
            worker_kwargs={
                "urdf_path": str(model.path),
                "collision_config": collision,
                "desired_torso_T_escape": desired_torso_T_escape,
                "desired_torso_T_hand": desired_torso_T_hand,
                "torso_T_board": torso_T_camera @ loaded_camera_T_board,
                "reference_full_q": loaded_activation.reference_state.position,
                "calibration_arm": plan["calibration_arm"],
                "plan_sha256": plan["content_sha256"],
                "recorded_at_utc": loaded_activation.reference_state.receipt_utc,
                "recorded_monotonic_s": (
                    loaded_activation.reference_state.receipt_monotonic_s
                ),
                "ik_config": IKConfig(restart_count=args.ik_restarts),
                "table_plane_config": table_plane_config,
            },
            driver=driver,
        )
        driver.check()
        _print_table_motion_preflight(loaded_activation, motion_preflight)

        # Planning can take several seconds.  Observe once more before motion
        # and reject a changed camera/board or supported cube instead of silently
        # turning this one-shot calibration test into feedback control.
        (
            verification_frames,
            verification_observation,
            verification_rejections,
        ) = _capture_controlled_table_observation(
            synchronized=synchronized,
            driver=driver,
            collect=lambda: _collect_new_camera_frames(
                rclpy,
                node,
                camera,
                frame_count=max(3, min(args.frame_count, 5)),
                timeout_s=args.camera_timeout_s,
                maximum_duration_s=args.maximum_burst_duration_s,
                control_check=driver.check,
            ),
            observe=lambda frames: _observe_table_frames(
                frames,
                camera_info=camera_info,
                hand_cube_detector=hand_cube_detector,
                board_detector=board_detector,
            ),
            label="post-replan loaded-state verification",
        )
        verified_camera_T_board = _observation_transform(
            verification_observation,
            "camera_T_board",
        )
        verified_board_T_cube = _observation_transform(
            verification_observation,
            "board_T_hand_cube",
        )
        board_shift = _transform_delta(
            loaded_camera_T_board,
            verified_camera_T_board,
        )
        if board_shift["translation_mm"] > args.maximum_board_shift_mm:
            raise ValueError(
                "loaded camera-to-board translation changed during planning by "
                f"{board_shift['translation_mm']:.3f}mm; limit is "
                f"{args.maximum_board_shift_mm:.3f}mm. No changing arm target "
                "was sent"
            )
        if board_shift["rotation_deg"] > args.maximum_board_shift_deg:
            raise ValueError(
                "loaded camera-to-board rotation changed during planning by "
                f"{board_shift['rotation_deg']:.3f}deg; limit is "
                f"{args.maximum_board_shift_deg:.3f}deg. No changing arm target "
                "was sent"
            )
        approval_cube_shift = _transform_delta(
            loaded_board_T_cube,
            verified_board_T_cube,
        )
        if approval_cube_shift["translation_mm"] > args.maximum_board_shift_mm:
            raise ValueError(
                "loaded supported cube moved during planning by "
                f"{approval_cube_shift['translation_mm']:.3f}mm; limit is "
                f"{args.maximum_board_shift_mm:.3f}mm. No changing arm target "
                "was sent"
            )
        if approval_cube_shift["rotation_deg"] > args.maximum_board_shift_deg:
            raise ValueError(
                "loaded supported cube rotated during planning by "
                f"{approval_cube_shift['rotation_deg']:.3f}deg; limit is "
                f"{args.maximum_board_shift_deg:.3f}deg. No changing arm target "
                "was sent"
            )

        final_activation = _wait_for_activation_handoff(
            synchronized,
            states,
            motion_preflight.pose_set,
            recording,
        )
        escape_target_q = np.asarray(
            motion_preflight.escape_ik_solution.calibration_q,
            dtype=np.float64,
        )
        table_target_q = np.asarray(
            motion_preflight.target_ik_solution.calibration_q,
            dtype=np.float64,
        )
        (
            final_report,
            final_escape_clearance,
            final_elevated_route_clearance,
        ) = _run_isolated_control_work(
            label="final loaded-state route validation",
            worker=_validate_final_table_motion_worker,
            worker_kwargs={
                "urdf_path": str(model.path),
                "collision_config": collision,
                "pose_set": motion_preflight.pose_set,
                "reference_full_q": final_activation.reference_state.position,
                "torso_T_board": torso_T_camera @ verified_camera_T_board,
                "calibration_arm": plan["calibration_arm"],
                "escape_target_q": escape_target_q,
                "table_target_q": table_target_q,
                "table_plane_config": table_plane_config,
            },
            driver=driver,
        )
        if not final_escape_clearance.passed:
            raise ValueError(
                "post-takeover supported-start escape either deepens the modeled "
                "table contact or does not finish clear of the table plane. No "
                "changing arm target was sent"
            )
        if not final_elevated_route_clearance.passed:
            raise ValueError(
                "post-takeover elevated route puts "
                f"{final_elevated_route_clearance.minimum_link} only "
                f"{final_elevated_route_clearance.minimum_clearance_m:.4f}m above "
                "the table plane; require "
                f"{final_elevated_route_clearance.required_clearance_m:.4f}m. No "
                "changing arm target was sent"
            )
        driver.check()
        synchronized.install_validated_plan(
            pose_set=motion_preflight.pose_set,
            approved_validation_report_sha256=final_report.content_sha256,
            validated_reference_state=final_activation.reference_state,
        )
        driver.check()
        _print_dynamic_preflight(final_activation, final_report)
        print(
            "POST-TAKEOVER PLAN INSTALLED — beginning the validated one-shot "
            "open-loop motion now; the achieved image is used only for scoring, "
            "never for endpoint correction"
        )
        escape_outbound_started_s = time.monotonic()
        synchronized.start_pose(
            TABLE_ESCAPE_POSE_ID,
            approval=final_report.approval(
                HANDOFF_POSE_ID,
                TABLE_ESCAPE_POSE_ID,
            ),
            operator_confirmed=True,
        )
        _wait_for_driven_state(
            synchronized,
            driver,
            ExecutorState.READY,
            rclpy=rclpy,
            node=node,
            timeout_s=executor_config.motion_timeout_s + 5.0,
        )
        escape_outbound_duration_s = time.monotonic() - escape_outbound_started_s
        attained_escape_outbound = synchronized.observe_state()
        synchronized.start_pose(
            TABLE_TARGET_POSE_ID,
            approval=final_report.approval(
                TABLE_ESCAPE_POSE_ID,
                TABLE_TARGET_POSE_ID,
            ),
            operator_confirmed=True,
        )
        _wait_for_driven_state(
            synchronized,
            driver,
            ExecutorState.READY,
            rclpy=rclpy,
            node=node,
            timeout_s=executor_config.motion_timeout_s + 5.0,
        )
        attained_target_before_capture = synchronized.observe_state()
        # The complete command-space route, including both return edges, was
        # validated from the loaded state after ownership and before this first
        # changing target. Keep the nominal command at the target, capture, then
        # traverse those same segments in reverse. Do not create a different
        # return segment by rebasing on the measured tracking offset.
        synchronized.begin_capture()
        try:
            achieved_frames = _collect_new_camera_frames(
                rclpy,
                node,
                camera,
                frame_count=args.frame_count,
                timeout_s=args.camera_timeout_s,
                maximum_duration_s=args.maximum_burst_duration_s,
                control_check=driver.check,
            )
        except KeyboardInterrupt:
            if synchronized.state is ExecutorState.CAPTURING:
                synchronized.finish_capture(outcome="operator interrupted capture")
            raise
        except Exception as error:  # noqa: BLE001 - any visual failure is unscored.
            if synchronized.state is ExecutorState.CAPTURING:
                synchronized.finish_capture(outcome="visual capture failed")
            # A control-thread error is not a recoverable data-quality failure.
            # Re-raise it so the ownership cleanup runs immediately.
            driver.check()
            capture_failure = f"{type(error).__name__}: {error}"
            print(
                "TABLE IMAGE CAPTURE INVALID — completing the validated reverse "
                "motion before clean release; this trial will not produce an "
                "accuracy score"
            )
        else:
            synchronized.finish_capture(outcome="captured lossless table burst")
        attained_target_after_capture = synchronized.observe_state()
        target_capture_position_spread_rad = float(
            np.max(
                np.abs(
                    attained_target_after_capture.position
                    - attained_target_before_capture.position
                )
            )
        )
        synchronized.start_pose(
            TABLE_ESCAPE_POSE_ID,
            approval=final_report.approval(
                TABLE_TARGET_POSE_ID,
                TABLE_ESCAPE_POSE_ID,
            ),
            operator_confirmed=True,
        )
        _wait_for_driven_state(
            synchronized,
            driver,
            ExecutorState.READY,
            rclpy=rclpy,
            node=node,
            timeout_s=executor_config.motion_timeout_s + 5.0,
        )
        attained_escape_return = synchronized.observe_state()
        supported_return_timeout_s = (
            escape_outbound_duration_s
            + executor_config.acquisition_ramp_s
            + executor_config.settle_dwell_s
        )
        synchronized.start_pose(
            HANDOFF_POSE_ID,
            approval=final_report.approval(
                TABLE_ESCAPE_POSE_ID,
                HANDOFF_POSE_ID,
            ),
            operator_confirmed=True,
        )
        _wait_for_driven_state(
            synchronized,
            driver,
            ExecutorState.READY,
            rclpy=rclpy,
            node=node,
            timeout_s=supported_return_timeout_s,
        )
        attained_supported_return = synchronized.observe_state()
        # Stop rt/lowcmd before asking PC2 to select the AI motion service.  The
        # watchdog remains armed during this no-command handoff interval.
        driver.close()
        driver.check()
        dex3_controller.timeout()
        watchdog.restore_seated()
        synchronized.confirm_external_takeover(
            "PC2 verified AI takeover through FSM 0 -> 1 -> seated FSM 3"
        )
        print(
            "returned to the measured table-supported pose; PC2 verified "
            "AI FSM 0 -> 1 -> seated FSM 3 before debug lowcmd closed"
        )
    except BaseException as error:
        primary_error = error
        raise
    finally:
        cleanup_errors: list[tuple[str, BaseException]] = []
        if driver is not None and driver.is_alive:
            _attempt_safety_cleanup(
                cleanup_errors,
                "control driver stop",
                driver.close,
            )
        local_dex3_timeout_error = None
        if dex3_controller is not None and not dex3_controller.timed_out:
            try:
                dex3_controller.timeout()
            except BaseException as error:  # noqa: BLE001 - finish PC2 recovery.
                local_dex3_timeout_error = error

        def finish_guard_ownership() -> None:
            if watchdog is None:
                return
            if not (
                watchdog.armed
                or (transport is not None and transport.requires_external_takeover)
            ):
                return
            if transport is None:
                watchdog.disarm()
                return
            _terminate_debug_lowcmd_safely(
                watchdog,
                synchronized,
                transport,
                reason="table-accuracy debug lowcmd failed or was interrupted",
            )

        _attempt_safety_cleanup(
            cleanup_errors,
            "PC2/controller ownership handoff",
            finish_guard_ownership,
        )

        def close_dex3_control() -> None:
            if dex3_controller is None:
                return
            if (
                not dex3_controller.timed_out
                and watchdog is not None
                and (watchdog.terminal_action is not None)
            ):
                dex3_controller.close_after_external_timeout()
            else:
                dex3_controller.close()

        _attempt_safety_cleanup(
            cleanup_errors,
            "Dex3 controller close",
            close_dex3_control,
        )
        if local_dex3_timeout_error is not None and (
            watchdog is None or watchdog.terminal_action is None
        ):
            cleanup_errors.append(("local Dex3 timeout", local_dex3_timeout_error))

        def close_unowned_transport() -> None:
            if transport is not None and not transport.requires_external_takeover:
                transport.close()

        _attempt_safety_cleanup(
            cleanup_errors,
            "unowned debug transport close",
            close_unowned_transport,
        )
        if watchdog is not None and (watchdog.armed and transport is None):
            _attempt_safety_cleanup(
                cleanup_errors,
                "orphaned watchdog disarm",
                watchdog.disarm,
            )
        if observer is not None:
            _attempt_safety_cleanup(
                cleanup_errors,
                "lowstate observer close",
                observer.close,
            )
        if dex3_observer is not None:
            _attempt_safety_cleanup(
                cleanup_errors,
                "Dex3 observer close",
                dex3_observer.close,
            )
        if camera is not None:
            _attempt_safety_cleanup(
                cleanup_errors,
                "camera close",
                camera.close,
            )
        _attempt_safety_cleanup(cleanup_errors, "ROS node destroy", node.destroy_node)
        _attempt_safety_cleanup(
            cleanup_errors,
            "ROS shutdown",
            lambda: _shutdown_rclpy_once(rclpy),
        )
        _attempt_safety_cleanup(
            cleanup_errors,
            "command lock release",
            command_lock.release,
        )
        if primary_error is not None:
            _attempt_safety_cleanup(
                cleanup_errors,
                "table failure evidence write",
                lambda: _write_table_failure_bundle(
                    output=output,
                    error=primary_error,
                    plan=plan,
                    input_plan=input_plan,
                    hardware_bytes=hardware_bytes,
                    collision_bytes=collision_bytes,
                    preflight_frames=preflight_frames,
                    loaded_planning_frames=loaded_planning_frames,
                    verification_frames=verification_frames,
                    achieved_frames=achieved_frames,
                    motion_preflight=motion_preflight,
                    final_report=final_report,
                    synchronized=synchronized,
                    watchdog=watchdog,
                    transport=transport,
                    attained_states={
                        "lifted_start_outbound": attained_escape_outbound,
                        "table_target_before_capture": (attained_target_before_capture),
                        "table_target_after_capture": attained_target_after_capture,
                        "lifted_start_return": attained_escape_return,
                        "supported_return": attained_supported_return,
                    },
                    cleanup_errors=cleanup_errors,
                ),
            )
        _raise_safety_cleanup_failures(primary_error, cleanup_errors)

    assert initial_observation is not None
    assert loaded_planning_observation is not None
    assert verification_observation is not None
    assert execution_plan is not None
    assert motion_preflight is not None
    assert final_report is not None
    assert final_escape_clearance is not None
    assert final_elevated_route_clearance is not None
    assert final_activation is not None
    assert board_shift is not None
    assert initial_cube_shift is not None
    assert takeover_board_shift is not None
    assert takeover_cube_shift is not None
    assert approval_cube_shift is not None
    assert escape_outbound_duration_s is not None
    assert supported_return_timeout_s is not None
    assert attained_escape_outbound is not None
    assert attained_target_before_capture is not None
    assert attained_target_after_capture is not None
    assert attained_escape_return is not None
    assert attained_supported_return is not None
    assert target_capture_position_spread_rad is not None
    assert dex3_posture_evidence is not None
    gravity_reference_q = gravity_feedforward.reference_full_q
    takeover_q14 = np.concatenate(
        (gravity_reference_q[15:22], gravity_reference_q[22:29])
    )
    takeover_gravity_tau = gravity_feedforward.torque_for(takeover_q14)
    escape_command_q14 = takeover_q14.copy()
    table_command_q14 = takeover_q14.copy()
    calibration_slice = (
        slice(0, 7) if plan["calibration_arm"] == "left" else slice(7, 14)
    )
    escape_command_q14[calibration_slice] = escape_target_q
    table_command_q14[calibration_slice] = table_target_q
    escape_gravity_tau = gravity_feedforward.torque_for(escape_command_q14)
    table_gravity_tau = gravity_feedforward.torque_for(table_command_q14)
    preflight_manifest = _write_table_image_burst(
        output / "preflight",
        preflight_frames,
        commands_robot=False,
    )
    loaded_planning_manifest = _write_table_image_burst(
        output / "loaded_planning",
        loaded_planning_frames,
        commands_robot=True,
    )
    verification_manifest = _write_table_image_burst(
        output / "loaded_verification",
        verification_frames,
        commands_robot=True,
    )
    achieved_manifest = None
    evaluation = None
    evaluation_failure = capture_failure
    if achieved_frames:
        achieved_manifest = _write_table_image_burst(
            output / "achieved",
            achieved_frames,
            commands_robot=True,
        )
        if evaluation_failure is None:
            try:
                achieved_observation = observe_burst(
                    sorted((output / "achieved").glob("frame_*.png")),
                    camera_info=camera_info,
                    hand_cube_detector=hand_cube_detector,
                    board_detector=board_detector,
                    minimum_accepted_frames=3,
                    reject_unstable=False,
                )
                measured_capture_q = 0.5 * (
                    attained_target_before_capture.position
                    + attained_target_after_capture.position
                )
                torso_T_hand_at_measured_q = model.transform(
                    "torso_link",
                    arm_hand_link(plan["calibration_arm"]),
                    dict(
                        zip(
                            G1_29_JOINT_NAMES,
                            measured_capture_q,
                            strict=True,
                        )
                    ),
                )
                predicted_board_T_cube = predicted_board_T_cube_from_model(
                    torso_T_camera=torso_T_camera,
                    hand_T_cube=hand_T_cube,
                    camera_T_board=_observation_transform(
                        achieved_observation,
                        "camera_T_board",
                    ),
                    torso_T_hand_at_measured_q=torso_T_hand_at_measured_q,
                )
                evaluation = create_evaluation_document(
                    plan=plan,
                    achieved_burst=achieved_observation,
                    predicted_board_T_cube=predicted_board_T_cube,
                )
            except Exception as error:  # noqa: BLE001 - preserve scoring failure.
                evaluation_failure = f"{type(error).__name__}: {error}"
    if evaluation_failure is not None:
        failure_document = {
            "schema_version": 1,
            "kind": "g1_table_accuracy_evaluation_failure",
            "plan_sha256": plan["content_sha256"],
            "reason": evaluation_failure,
            "motion_completed_safely": True,
        }
        failure_document["content_sha256"] = _hardware_document_sha256(failure_document)
        _write_hardware_json(output / "evaluation_error.json", failure_document)
    (output / "pose_set.yaml").write_bytes(_pose_set_bytes(motion_preflight.pose_set))
    (output / "plan.json").write_text(
        json.dumps(plan, indent=2, sort_keys=True, allow_nan=False) + "\n",
        encoding="utf-8",
    )
    (output / "input_plan.json").write_text(
        json.dumps(input_plan, indent=2, sort_keys=True, allow_nan=False) + "\n",
        encoding="utf-8",
    )
    (output / "hardware.yaml").write_bytes(hardware_bytes)
    (output / "collision_pairs.yaml").write_bytes(collision_bytes)
    (output / "validation_report.json").write_bytes(
        _validation_report_bytes(final_report)
    )
    if evaluation is not None:
        _write_hardware_json(output / "evaluation.json", evaluation)
    runtime = {
        "schema_version": 3,
        "kind": "g1_table_accuracy_execution",
        "plan_sha256": plan["content_sha256"],
        "input_plan_sha256": input_plan["content_sha256"],
        "planning_policy": (
            "capture_loaded_state_and_build_ik_fcl_route_after_lowcmd_ownership"
        ),
        "final_validation_report_sha256": final_report.content_sha256,
        "hardware_config_sha256": hashlib.sha256(hardware_bytes).hexdigest(),
        "collision_config_sha256": collision.content_sha256,
        "table_plane_config": {
            name: getattr(table_plane_config, name)
            for name in table_plane_config.__dataclass_fields__
        },
        "escape_target": {
            "desired_board_T_hand_cube": desired_board_T_escape.tolist(),
            "desired_torso_T_hand": desired_torso_T_escape.tolist(),
            "policy": "preserve_live_xy_orientation_and_lift_to_planned_relative_z",
        },
        "motion_preflight": motion_preflight.to_dict(),
        "final_escape_clearance": final_escape_clearance.to_dict(),
        "final_elevated_route_clearance": final_elevated_route_clearance.to_dict(),
        "final_activation_state": final_activation.reference_state.to_dict(),
        "final_activation_readiness": final_activation.readiness.to_dict(),
        "gravity_feedforward": {
            "implementation": "pinocchio_rnea_at_commanded_q",
            "upstream_reference": UNITREE_XR_GRAVITY_REFERENCE,
            "pinocchio_version": gravity_feedforward.backend_version,
            "urdf_sha256": gravity_feedforward.urdf_sha256,
            "velocity_rad_s": [0.0] * 29,
            "acceleration_rad_s2": [0.0] * 29,
            "non_arm_reference": "measured_seated_takeover_configuration",
            "reference_full_q": gravity_reference_q.tolist(),
            "external_payload_model": "none",
            "lowcmd_torque_ramp": "command_weight_zero_to_one_during_acquisition",
            "takeover_tau14_nm": takeover_gravity_tau.tolist(),
            "escape_tau14_nm": escape_gravity_tau.tolist(),
            "table_target_tau14_nm": table_gravity_tau.tolist(),
        },
        "dex3_posture_control": {
            "posture_name": "nvidia_groot_middle_close",
            "posture_source": DEX3_CALIBRATION_POSTURE_SOURCE,
            "left_commanded_q_rad": list(dex3_controller.config.left_target_q_rad),
            "right_commanded_q_rad": list(dex3_controller.config.right_target_q_rad),
            "measured_settled_state": dex3_posture_evidence.to_dict(),
            "terminal_policy": "unitree_timeout_bit_on_both_hands",
        },
        "loaded_planning_to_verification_camera_shift": board_shift,
        "planned_to_live_initial_cube_shift": initial_cube_shift,
        "takeover_camera_to_board_shift": takeover_board_shift,
        "takeover_board_to_cube_shift": takeover_cube_shift,
        "loaded_planning_to_verification_cube_shift": approval_cube_shift,
        "escape_outbound_duration_s": escape_outbound_duration_s,
        "supported_return_timeout_s": supported_return_timeout_s,
        "preflight_observation": initial_observation,
        "loaded_planning_observation": loaded_planning_observation,
        "loaded_planning_rejections": list(loaded_planning_rejections),
        "loaded_verification_observation": verification_observation,
        "loaded_verification_rejections": list(verification_rejections),
        "capture_manifests": {
            "preflight_sha256": preflight_manifest["content_sha256"],
            "loaded_planning_sha256": loaded_planning_manifest["content_sha256"],
            "loaded_verification_sha256": verification_manifest["content_sha256"],
            "achieved_sha256": (
                None
                if achieved_manifest is None
                else achieved_manifest["content_sha256"]
            ),
        },
        "evaluation_status": (
            "failed"
            if evaluation is None
            else (
                "passed"
                if evaluation["measurement_quality"]["passed"]
                else "measured_with_repeatability_warning"
            )
        ),
        "evaluation_failure": evaluation_failure,
        "endpoint_policy": "measured_stationarity_with_tracking_error_recorded",
        "capture_policy": "capture_immediately_after_target_settle_before_return",
        "command_path_policy": (
            "post_takeover_loaded_state_plan_then_prevalidated_nominal_segments_"
            "reversed_without_endpoint_visual_correction"
        ),
        "endpoint_tracking_evidence": {
            "lifted_start_outbound": _joint_endpoint_evidence(
                sample=attained_escape_outbound,
                target_q=escape_target_q,
                calibration_arm=plan["calibration_arm"],
            ),
            "table_target_before_capture": _joint_endpoint_evidence(
                sample=attained_target_before_capture,
                target_q=table_target_q,
                calibration_arm=plan["calibration_arm"],
            ),
            "table_target_after_capture": _joint_endpoint_evidence(
                sample=attained_target_after_capture,
                target_q=table_target_q,
                calibration_arm=plan["calibration_arm"],
            ),
            "lifted_start_return": _joint_endpoint_evidence(
                sample=attained_escape_return,
                target_q=escape_target_q,
                calibration_arm=plan["calibration_arm"],
            ),
            "supported_return": _joint_endpoint_evidence(
                sample=attained_supported_return,
                target_q=final_activation.handoff_q,
                calibration_arm=plan["calibration_arm"],
            ),
            "maximum_full_joint_change_during_capture_rad": (
                target_capture_position_spread_rad
            ),
        },
        "executor_events": [_executor_event_dict(item) for item in synchronized.events],
        "terminal_state": synchronized.state.value,
        "terminal_external_takeover_verified": watchdog.terminal_action
        in {"seated", "zero_torque"},
        "terminal_watchdog_action": watchdog.terminal_action,
        "verified_zero_torque": watchdog.terminal_action == "zero_torque",
        "verified_seated": watchdog.terminal_action == "seated",
        "returned_to_dynamic_handoff": (
            synchronized.current_pose_id == HANDOFF_POSE_ID
        ),
        "commands_robot": True,
    }
    runtime["content_sha256"] = _hardware_document_sha256(runtime)
    _write_hardware_json(output / "runtime.json", runtime)
    result = {
        "output": str(output),
        "plan_sha256": plan["content_sha256"],
        "terminal_external_takeover_verified": watchdog.terminal_action
        in {"seated", "zero_torque"},
        "verified_zero_torque": watchdog.terminal_action == "zero_torque",
        "verified_seated": watchdog.terminal_action == "seated",
        "returned_to_dynamic_handoff": True,
        "evaluation_status": (
            "failed"
            if evaluation is None
            else (
                "passed"
                if evaluation["measurement_quality"]["passed"]
                else "measured_with_repeatability_warning"
            )
        ),
    }
    if evaluation is not None:
        result["evaluation_sha256"] = evaluation["content_sha256"]
        result.update(evaluation["task_error"])
        result["measurement_quality"] = evaluation["measurement_quality"]
        result["model_implied_tracking_error"] = evaluation[
            "model_implied_tracking_error"
        ]
        result["held_out_composite_model_error"] = evaluation[
            "held_out_composite_model_error"
        ]
    else:
        result["evaluation_error"] = evaluation_failure
    print(json.dumps(result, indent=2, sort_keys=True))
    return 0 if evaluation is not None else 1


def _validate_table_execution_arguments(args: argparse.Namespace) -> None:
    if args.frame_count < 3:
        raise ValueError("--frame-count must be at least 3")
    if args.camera_timeout_s <= 0:
        raise ValueError("--camera-timeout-s must be positive")
    if args.maximum_burst_duration_s <= 0:
        raise ValueError("--maximum-burst-duration-s must be positive")
    if args.ik_restarts < 1:
        raise ValueError("--ik-restarts must be positive")
    if args.minimum_board_clearance_mm <= 0:
        raise ValueError("--minimum-board-clearance-mm must be positive")
    if args.maximum_board_shift_mm <= 0:
        raise ValueError("--maximum-board-shift-mm must be positive")
    if args.maximum_board_shift_deg <= 0:
        raise ValueError("--maximum-board-shift-deg must be positive")


def _validate_table_plan_artifacts(plan: dict, *, model: URDFModel) -> None:
    if plan["sources"]["urdf_sha256"] != model.sha256:
        raise ValueError("table-accuracy plan belongs to a different URDF")
    hand_cube_path = Path(plan["sources"]["hand_cube_config_path"])
    if not hand_cube_path.is_file():
        raise FileNotFoundError(
            f"hand-cube config from plan is missing: {hand_cube_path}"
        )
    hand_cube_sha256 = hashlib.sha256(hand_cube_path.read_bytes()).hexdigest()
    if hand_cube_sha256 != plan["sources"]["hand_cube_config_sha256"]:
        raise ValueError("hand-cube config has changed since the plan was created")


def _collect_new_camera_frames(
    rclpy,
    node,
    camera,
    *,
    frame_count: int,
    timeout_s: float,
    maximum_duration_s: float,
    control_check=None,
) -> tuple[ROSImageFrame, ...]:
    """Collect only frames received after this function is entered."""

    if frame_count < 1:
        raise ValueError("camera frame count must be positive")
    if timeout_s <= 0 or maximum_duration_s <= 0:
        raise ValueError("camera timing limits must be positive")
    existing = camera.frames.snapshot()
    seen = {
        (item.timing.receipt_monotonic_s, item.timing.header_stamp_ns)
        for item in existing
    }
    expected_profile = None if not existing else existing[-1].camera_info.profile_sha256
    collected: list[ROSImageFrame] = []
    deadline = time.monotonic() + timeout_s
    while len(collected) < frame_count:
        if control_check is not None:
            control_check()
        if time.monotonic() >= deadline:
            raise RuntimeError(
                f"timed out after collecting {len(collected)}/{frame_count} "
                "new rectified camera frames"
            )
        rclpy.spin_once(node, timeout_sec=0.05)
        if control_check is not None:
            control_check()
        for frame in camera.frames.snapshot():
            key = (
                frame.timing.receipt_monotonic_s,
                frame.timing.header_stamp_ns,
            )
            if key in seen:
                continue
            seen.add(key)
            if expected_profile is None:
                expected_profile = frame.camera_info.profile_sha256
            if frame.camera_info.profile_sha256 != expected_profile:
                raise ValueError("camera profile changed during the image burst")
            collected.append(frame)
            if len(collected) == frame_count:
                break
        if len(collected) >= 2:
            duration = (
                collected[-1].timing.receipt_monotonic_s
                - collected[0].timing.receipt_monotonic_s
            )
            if duration > maximum_duration_s:
                raise RuntimeError(
                    f"camera burst duration is {duration:.3f}s; limit is "
                    f"{maximum_duration_s:.3f}s"
                )
    return tuple(collected)


def _retry_table_observation(
    *,
    collect: Callable[[], tuple[ROSImageFrame, ...]],
    observe: Callable[[tuple[ROSImageFrame, ...]], dict],
    label: str,
    maximum_attempts: int = 3,
) -> tuple[tuple[ROSImageFrame, ...], dict, tuple[str, ...]]:
    """Retry a visual rejection without changing the robot target."""

    if not label:
        raise ValueError("table-observation retry label must be non-empty")
    if maximum_attempts < 1:
        raise ValueError("table-observation maximum attempts must be positive")
    rejections: list[str] = []
    for attempt in range(1, maximum_attempts + 1):
        frames = collect()
        try:
            observation = observe(frames)
        except ValueError as error:
            reason = str(error)
            rejections.append(reason)
            if attempt < maximum_attempts:
                print(
                    f"{label} burst {attempt}/{maximum_attempts} rejected: "
                    f"{reason}; collecting a fresh burst before any changing target"
                )
                continue
            raise ValueError(
                f"{label} failed after {maximum_attempts} fresh bursts; "
                f"last rejection: {reason}"
            ) from error
        return frames, observation, tuple(rejections)
    raise AssertionError("unreachable table-observation retry state")


def _capture_controlled_table_observation(
    *,
    synchronized: SynchronizedPoseExecutor,
    driver: ExecutorControlDriver,
    collect: Callable[[], tuple[ROSImageFrame, ...]],
    observe: Callable[[tuple[ROSImageFrame, ...]], dict],
    label: str,
) -> tuple[tuple[ROSImageFrame, ...], dict, tuple[str, ...]]:
    """Capture while the fixed-rate driver holds one unchanged command target."""

    synchronized.begin_capture()
    try:
        result = _retry_table_observation(
            collect=collect,
            observe=observe,
            label=label,
        )
    except BaseException:
        if synchronized.state is ExecutorState.CAPTURING:
            synchronized.finish_capture(outcome=f"{label} failed")
        driver.check()
        raise
    synchronized.finish_capture(outcome=f"{label} accepted")
    driver.check()
    return result


def _write_table_image_burst(
    output: Path,
    frames: tuple[ROSImageFrame, ...],
    *,
    commands_robot: bool = False,
) -> dict:
    if not frames:
        raise ValueError("cannot write an empty table image burst")
    if output.exists():
        raise FileExistsError(f"table image burst already exists: {output}")
    profiles = {item.camera_info.profile_sha256 for item in frames}
    if len(profiles) != 1:
        raise ValueError("table image burst mixes camera profiles")
    output.mkdir(parents=True)
    records = []
    for index, frame in enumerate(frames, start=1):
        name = f"frame_{index:03d}.png"
        ok, encoded = cv2.imencode(
            ".png",
            frame.image_bgr,
            [cv2.IMWRITE_PNG_COMPRESSION, 3],
        )
        if not ok:
            raise RuntimeError(f"failed to losslessly encode table frame {index}")
        content = encoded.tobytes()
        (output / name).write_bytes(content)
        records.append(
            {
                "file": name,
                "sha256": hashlib.sha256(content).hexdigest(),
                "receipt_monotonic_s": frame.timing.receipt_monotonic_s,
                "receipt_utc": frame.timing.receipt_utc,
                "header_stamp_ns": frame.timing.header_stamp_ns,
            }
        )
    duration_s = (
        frames[-1].timing.receipt_monotonic_s - frames[0].timing.receipt_monotonic_s
    )
    manifest = {
        "schema_version": 1,
        "kind": "g1_table_accuracy_image_burst",
        "created_at_utc": utc_now_iso(),
        "camera_info": frames[0].camera_info.to_dict(),
        "camera_profile_sha256": frames[0].camera_info.profile_sha256,
        "frame_count": len(frames),
        "duration_s": duration_s,
        "commands_robot": bool(commands_robot),
        "frames": records,
    }
    manifest["content_sha256"] = _hardware_document_sha256(manifest)
    _write_hardware_json(output / "manifest.json", manifest)
    return manifest


def _write_table_failure_bundle(
    *,
    output: Path,
    error: BaseException,
    plan: dict,
    input_plan: dict,
    hardware_bytes: bytes,
    collision_bytes: bytes,
    preflight_frames: tuple[ROSImageFrame, ...],
    loaded_planning_frames: tuple[ROSImageFrame, ...],
    verification_frames: tuple[ROSImageFrame, ...],
    achieved_frames: tuple[ROSImageFrame, ...],
    motion_preflight,
    final_report,
    synchronized,
    watchdog,
    transport,
    attained_states: dict,
    cleanup_errors: list[tuple[str, BaseException]],
) -> None:
    """Persist a failed physical trial after command ownership cleanup completes."""

    if output.exists():
        raise FileExistsError(f"table failure output already exists: {output}")
    output.mkdir(parents=True)
    manifests = {}
    for name, frames, commands_robot in (
        ("preflight", preflight_frames, False),
        ("loaded_planning", loaded_planning_frames, True),
        ("loaded_verification", verification_frames, True),
        ("achieved", achieved_frames, True),
    ):
        if frames:
            manifests[name] = _write_table_image_burst(
                output / name,
                frames,
                commands_robot=commands_robot,
            )["content_sha256"]
    (output / "plan.json").write_text(
        json.dumps(plan, indent=2, sort_keys=True, allow_nan=False) + "\n",
        encoding="utf-8",
    )
    (output / "input_plan.json").write_text(
        json.dumps(input_plan, indent=2, sort_keys=True, allow_nan=False) + "\n",
        encoding="utf-8",
    )
    (output / "hardware.yaml").write_bytes(hardware_bytes)
    (output / "collision_pairs.yaml").write_bytes(collision_bytes)
    if motion_preflight is not None:
        (output / "pose_set.yaml").write_bytes(
            _pose_set_bytes(motion_preflight.pose_set)
        )
    if final_report is not None:
        (output / "validation_report.json").write_bytes(
            _validation_report_bytes(final_report)
        )
    document = {
        "schema_version": 3,
        "kind": "g1_table_accuracy_execution_failure",
        "occurred_at_utc": utc_now_iso(),
        "plan_sha256": plan["content_sha256"],
        "input_plan_sha256": input_plan["content_sha256"],
        "error": f"{type(error).__name__}: {error}",
        "commands_published": bool(
            transport is not None and transport.command_count > 0
        ),
        "command_count": None if transport is None else transport.command_count,
        "executor_state": (None if synchronized is None else synchronized.state.value),
        "executor_fault_reason": (
            None if synchronized is None else synchronized.fault_reason
        ),
        "executor_events": (
            []
            if synchronized is None
            else [_executor_event_dict(item) for item in synchronized.events]
        ),
        "terminal_watchdog_action": (
            None if watchdog is None else watchdog.terminal_action
        ),
        "attained_states": {
            name: None if sample is None else sample.to_dict()
            for name, sample in attained_states.items()
        },
        "capture_manifest_sha256": manifests,
        "cleanup_errors_before_failure_log": [
            {"action": action, "error": f"{type(item).__name__}: {item}"}
            for action, item in cleanup_errors
        ],
        "interpretation": (
            "failure evidence only; absence of an evaluation.json means no "
            "tabletop landing score was produced"
        ),
    }
    document["content_sha256"] = _hardware_document_sha256(document)
    _write_hardware_json(output / "failure.json", document)


def _observe_table_frames(
    frames: tuple[ROSImageFrame, ...],
    *,
    camera_info: RectifiedCameraInfo,
    hand_cube_detector: CorrespondenceDetector,
    board_detector: CharucoBoardPoseDetector,
) -> dict:
    with tempfile.TemporaryDirectory(prefix="g1-table-observation-") as temporary:
        directory = Path(temporary) / "burst"
        _write_table_image_burst(directory, frames)
        return observe_burst(
            sorted(directory.glob("frame_*.png")),
            camera_info=camera_info,
            hand_cube_detector=hand_cube_detector,
            board_detector=board_detector,
            minimum_accepted_frames=3,
        )


def _observation_transform(observation: dict, name: str) -> np.ndarray:
    try:
        raw = observation["aggregate"][name]
    except (KeyError, TypeError) as error:
        raise ValueError(f"table observation is missing aggregate {name}") from error
    return validate_transform(np.asarray(raw, dtype=np.float64))


def _transform_delta(first: np.ndarray, second: np.ndarray) -> dict[str, float]:
    first = validate_transform(first)
    second = validate_transform(second)
    translation_mm = 1000.0 * float(np.linalg.norm(second[:3, 3] - first[:3, 3]))
    relative = first[:3, :3].T @ second[:3, :3]
    rotation_deg = float(np.degrees(Rotation.from_matrix(relative.copy()).magnitude()))
    return {
        "translation_mm": translation_mm,
        "rotation_deg": rotation_deg,
    }


def _print_table_motion_preflight(
    activation: ActivationHandoff,
    motion_preflight,
) -> None:
    report = motion_preflight.validation_report
    clearances = [
        edge.minimum_clearance_m
        for edge in report.edges
        if edge.minimum_clearance_m is not None
    ]
    minimum_clearance = min(clearances) if clearances else None
    escape = motion_preflight.escape_ik_solution
    target = motion_preflight.target_ik_solution
    escape_clearance = motion_preflight.escape_clearance
    elevated_route_clearance = motion_preflight.elevated_route_clearance
    escape_joint_text = ", ".join(
        f"{name}={value:.4f}"
        for name, value in zip(
            arm_joint_names(motion_preflight.pose_set.calibration_arm),
            escape.calibration_q,
            strict=True,
        )
    )
    target_joint_text = ", ".join(
        f"{name}={value:.4f}"
        for name, value in zip(
            arm_joint_names(motion_preflight.pose_set.calibration_arm),
            target.calibration_q,
            strict=True,
        )
    )
    print(
        "LIVE SUPPORTED-START ROUTE PASSED IK + FCL: "
        f"escape IK error={escape.translation_error_m * 1000.0:.3f}mm/"
        f"{escape.rotation_error_deg:.3f}deg, "
        f"target IK error={target.translation_error_m * 1000.0:.3f}mm/"
        f"{target.rotation_error_deg:.3f}deg, "
        f"minimum clearance="
        f"{'n/a' if minimum_clearance is None else f'{minimum_clearance:.4f}m'}, "
        "escape destination board-plane clearance="
        f"{_optional_clearance(escape_clearance.destination_clearance_m)}, "
        "elevated-route board-plane clearance="
        f"{elevated_route_clearance.minimum_clearance_m:.4f}m "
        f"at {elevated_route_clearance.minimum_link}, "
        f"stationary samples={activation.readiness.sample_count}"
    )
    print("LIFTED START JOINTS — " + escape_joint_text)
    print("BOARD TARGET JOINTS — " + target_joint_text)


def _build_table_motion_preflight_worker(
    *,
    urdf_path: str,
    collision_config: CollisionConfig,
    desired_torso_T_escape: np.ndarray,
    desired_torso_T_hand: np.ndarray,
    torso_T_board: np.ndarray,
    reference_full_q: np.ndarray,
    calibration_arm: str,
    plan_sha256: str,
    recorded_at_utc: str,
    recorded_monotonic_s: float,
    ik_config: IKConfig,
    table_plane_config: TablePlaneConfig,
):
    """Build the heavy IK/FCL plan in a process isolated from control timing."""

    return build_table_motion_preflight(
        model=URDFModel(urdf_path),
        collision_config=collision_config,
        desired_torso_T_escape=desired_torso_T_escape,
        desired_torso_T_hand=desired_torso_T_hand,
        torso_T_board=torso_T_board,
        reference_full_q=reference_full_q,
        calibration_arm=calibration_arm,
        plan_sha256=plan_sha256,
        recorded_at_utc=recorded_at_utc,
        recorded_monotonic_s=recorded_monotonic_s,
        ik_config=ik_config,
        table_plane_config=table_plane_config,
    )


def _validate_final_table_motion_worker(
    *,
    urdf_path: str,
    collision_config: CollisionConfig,
    pose_set: PoseSet,
    reference_full_q: np.ndarray,
    torso_T_board: np.ndarray,
    calibration_arm: str,
    escape_target_q: np.ndarray,
    table_target_q: np.ndarray,
    table_plane_config: TablePlaneConfig,
) -> tuple[ValidationReport, object, object]:
    """Revalidate the exact loaded handoff and final observed table plane."""

    model = URDFModel(urdf_path)
    path_config = PathValidationConfig()
    report = PosePathValidator(
        model=model,
        collision_checker=FCLCollisionChecker(model, collision_config),
        config=path_config,
    ).validate(
        pose_set,
        directed_edges=(
            (HANDOFF_POSE_ID, TABLE_ESCAPE_POSE_ID),
            (TABLE_ESCAPE_POSE_ID, TABLE_TARGET_POSE_ID),
            (TABLE_TARGET_POSE_ID, TABLE_ESCAPE_POSE_ID),
            (TABLE_ESCAPE_POSE_ID, HANDOFF_POSE_ID),
        ),
        reference_full_q=reference_full_q,
    )
    if not report.passed:
        failures = [
            f"{edge.from_pose_id}->{edge.to_pose_id}: " + "; ".join(edge.failures)
            for edge in report.edges
            if not edge.passed
        ]
        raise ValueError("dynamic route validation failed: " + " | ".join(failures))
    escape_clearance = validate_table_plane_escape_path(
        model=model,
        collision_config=collision_config,
        torso_T_board=torso_T_board,
        reference_full_q=reference_full_q,
        calibration_arm=calibration_arm,
        target_calibration_q=escape_target_q,
        config=table_plane_config,
    )
    elevated_route_clearance = validate_table_plane_path(
        model=model,
        collision_config=collision_config,
        torso_T_board=torso_T_board,
        reference_full_q=reference_full_q,
        calibration_arm=calibration_arm,
        source_calibration_q=escape_target_q,
        target_calibration_q=table_target_q,
        config=table_plane_config,
    )
    return report, escape_clearance, elevated_route_clearance


def _validate_loaded_dex3_finger_sweep_worker(
    *,
    urdf_path: str,
    collision_config: CollisionConfig,
    body_q: np.ndarray,
    initial_left_hand_q_rad: np.ndarray,
    initial_right_hand_q_rad: np.ndarray,
    target_left_hand_q_rad: tuple[float, ...],
    target_right_hand_q_rad: tuple[float, ...],
    path_config: PathValidationConfig,
):
    """Run articulated Dex3 FCL away from the fixed-rate control process."""

    model = URDFModel(urdf_path)
    return validate_dex3_finger_sweep_at_state(
        model=model,
        collision_checker=FCLCollisionChecker(model, collision_config),
        body_q=body_q,
        initial_left_hand_q_rad=initial_left_hand_q_rad,
        initial_right_hand_q_rad=initial_right_hand_q_rad,
        target_left_hand_q_rad=target_left_hand_q_rad,
        target_right_hand_q_rad=target_right_hand_q_rad,
        config=path_config,
    )


def _run_isolated_control_work(
    *,
    label: str,
    worker: Callable,
    worker_kwargs: dict,
    driver: ExecutorControlDriver,
    control_maintenance: Callable[[], None] | None = None,
):
    """Poll control health while CPU/native planning runs in a spawned process."""

    if not label.strip():
        raise ValueError("isolated control-work label must be non-empty")
    pool = ProcessPoolExecutor(max_workers=1, mp_context=get_context("spawn"))
    future = pool.submit(worker, **worker_kwargs)
    started_s = time.monotonic()
    next_status_s = started_s + 5.0
    try:
        while True:
            try:
                result = future.result(
                    timeout=0.01 if control_maintenance is not None else 0.1
                )
                break
            except FuturesTimeoutError:
                driver.check()
                if control_maintenance is not None:
                    control_maintenance()
                now = time.monotonic()
                if now >= next_status_s:
                    print(
                        f"{label} still running after {now - started_s:.1f}s; "
                        "the fixed-rate controller is holding the unchanged target"
                    )
                    next_status_s = now + 5.0
        driver.check()
    except BaseException:
        future.cancel()
        pool.shutdown(wait=future.done(), cancel_futures=True)
        raise
    pool.shutdown(wait=True)
    return result


def _optional_clearance(value: float | None) -> str:
    return "no moving geometry" if value is None else f"{value:.4f}m"


def _executor_event_dict(event) -> dict:
    return {
        "sequence": event.sequence,
        "occurred_monotonic_s": event.occurred_monotonic_s,
        "previous_state": event.previous_state.value,
        "state": event.state.value,
        "reason": event.reason,
    }


def _hardware_document_sha256(document: dict) -> str:
    return hashlib.sha256(
        json.dumps(
            document,
            sort_keys=True,
            separators=(",", ":"),
            allow_nan=False,
        ).encode()
    ).hexdigest()


def _write_hardware_json(path: Path, document: dict) -> None:
    path.parent.mkdir(parents=True, exist_ok=True)
    path.write_text(
        json.dumps(document, indent=2, sort_keys=True, allow_nan=False) + "\n",
        encoding="utf-8",
    )


def run_commission_weight_zero(args: argparse.Namespace) -> int:
    _require_ack(args.confirm, WRITE_ACK)
    if args.timeout_s <= 0:
        raise ValueError("--timeout-s must be positive")
    clock = SystemClock()
    with CommandOwnerLock(args.lock_file):
        transport = UnitreeArmSDKTransport(_transport_config(args), clock=clock)
        try:
            state = _wait_for_state(transport, args.timeout_s)
            command = ArmCommand.create(
                [*state.left_q, *state.right_q],
                weight=0.0,
                issued_monotonic_s=clock.monotonic(),
            )
            transport.send_command(command)
        finally:
            transport.close()
    print("weight-zero arm_sdk packet published and transport closed")
    return 0


def run_commission_damping(args: argparse.Namespace) -> int:
    """Verify the actual supported damping transition without arm ownership."""

    _require_ack(args.confirm, DAMP_ACK)
    observer = UnitreeLowStateObserver(_transport_config(args))
    watchdog = _pc2_damping_watchdog(
        args,
        args.hardware_config,
        require_regular=False,
    )
    try:
        initial = _wait_for_state(observer, 5.0)
        watchdog.start()
        print(
            f"PC2 damping watchdog armed from mode_machine={initial.mode_machine}; "
            f"trigger={args.trigger}"
        )
        if args.trigger == "heartbeat-timeout":
            watchdog.wait_for_automatic_damping()
        else:
            watchdog.damp("explicit physical commissioning test")
        print(
            "physical damping commissioning passed; locomotion fsm_id=1 "
            f"(mode_machine remains {initial.mode_machine})"
        )
        return 0
    except BaseException:
        if watchdog.armed:
            watchdog.damp("damping commissioning interrupted")
        raise
    finally:
        observer.close()


def run_commission_dex3_middle_close(args: argparse.Namespace) -> int:
    """Commission middle-close only after a live-derived clearance route."""

    _require_ack(args.confirm, MOTION_ACK)
    if args.duration_s <= 0.0:
        raise ValueError("--duration-s must be positive")
    states = StateSampleBuffer()
    lowstate = None
    dex3_observer = None
    dex3_controller = None
    transport = None
    synchronized = None
    driver = None
    watchdog = None
    primary_error = None
    cleanup_errors: list[tuple[str, BaseException]] = []
    with CommandOwnerLock(args.lock_file):
        try:
            collision = _validate_collision_preflight(args.collision_config)
            recording, _, executor_config, rate_hz = _runtime_configs(
                args.hardware_config
            )
            pose_set = _hardware_pose_set(args.hardware_config)
            lowstate = UnitreeLowStateObserver(
                _transport_config(args), on_sample=states.add
            )
            dex3_config = _dex3_control_config(args)
            base_path_config = PathValidationConfig()
            dex3_observer = UnitreeDex3StateObserver(
                dex3_config,
                initialize_factory=False,
            )
            activation = _wait_for_activation_handoff(
                lowstate,
                states,
                pose_set,
                recording,
            )
            initial_hands = _wait_for_dex3_state(dex3_observer, 5.0)
            model = URDFModel(_configured_urdf(args.hardware_config))
            dex3_model = URDFModel(_configured_gravity_urdf(args.hardware_config))
            live_collision = live_dex3_collision_config(collision)
            print(
                "READ-ONLY DEX3 CLEARANCE PLANNING — searching outward from the "
                "fresh stationary shoulder positions and checking the complete "
                "measured-to-target finger sweep; no command publisher exists",
                flush=True,
            )
            clearance_plan = plan_dual_arm_shoulder_clearance(
                model=model,
                collision_checker=FCLCollisionChecker(model, collision),
                dex3_model=dex3_model,
                dex3_collision_checker=FCLCollisionChecker(dex3_model, live_collision),
                reference_full_q=activation.reference_state.position,
                initial_left_hand_q_rad=initial_hands.left.position,
                initial_right_hand_q_rad=initial_hands.right.position,
                target_left_hand_q_rad=dex3_config.left_target_q_rad,
                target_right_hand_q_rad=dex3_config.right_target_q_rad,
                path_config=base_path_config,
                progress=lambda index, total, offset: print(
                    "READ-ONLY DEX3 CLEARANCE PLANNING: candidate "
                    f"{index}/{total}, outward offset={offset:.4f}rad; NO MOTION",
                    flush=True,
                ),
                rejection=lambda offset, reason: print(
                    "READ-ONLY DEX3 CLEARANCE REJECTED: "
                    f"outward offset={offset:.4f}rad; {reason}; NO MOTION",
                    flush=True,
                ),
            )
            left_target = clearance_plan.dual_clearance_q14[1]
            right_target = clearance_plan.dual_clearance_q14[8]
            pair = clearance_plan.finger_sweep_minimum_pair
            pair_text = "unknown" if pair is None else "/".join(pair)
            recovery = clearance_plan.finger_sweep_recovered_start_limit_joints
            recovery_text = "none" if not recovery else ",".join(recovery)
            print(
                "READ-ONLY DEX3 CLEARANCE PLAN PASSED — derived from the live "
                "stationary Ready state and measured finger joints; selected "
                "the first valid candidate from the 0.0800rad outward search start; "
                f"outward shoulder-roll offset="
                f"{clearance_plan.shoulder_roll_offset_rad:.4f}rad; "
                f"left target={left_target:.4f}rad, right target="
                f"{right_target:.4f}rad; arm-route minimum clearance="
                f"{clearance_plan.minimum_clearance_m:.4f}m; complete finger-sweep "
                f"minimum clearance={clearance_plan.finger_sweep_minimum_clearance_m:.4f}m "
                f"at {pair_text} across "
                f"{clearance_plan.finger_sweep_sample_count} samples; measured "
                f"start-limit recovery={recovery_text}"
            )
            _wait_for_space(
                "No command publisher exists yet. Verify the harness and complete "
                "validated shoulder/finger sweep are clear. Press SPACE to acquire the "
                "hands and arms at their exact measured states, hold the fingers "
                "through the validated right-then-left shoulder route, close and "
                "test both hands, restore and hold the measured finger posture "
                "through the reverse arm route, and release arm_sdk: "
            )
            gravity_feedforward = _prepare_gravity_feedforward(
                args.hardware_config,
                activation.reference_state.position,
            )
            transport = UnitreeArmSDKTransport(
                _transport_config(args), observer=lowstate
            )
            lowstate = None
            dex3_controller = UnitreeDex3PostureController(
                dex3_config,
                observer=dex3_observer,
            )
            dex3_observer = None
            watchdog = _pc2_damping_watchdog(args, args.hardware_config)
            raw_executor = DualArmClearanceExecutor(
                transport=transport,
                clock=SystemClock(),
                plan=clearance_plan,
                config=executor_config,
                gravity_feedforward=gravity_feedforward,
            )
            synchronized = SynchronizedPoseExecutor(raw_executor)
            driver = ExecutorControlDriver(
                synchronized,
                rate_hz=rate_hz,
                safety_heartbeat=watchdog.pulse,
            )
            watchdog.start()
            held_hands = dex3_controller.acquire_measured_hold(
                safety_heartbeat=watchdog.pulse,
            )
            held_error = max(
                held_hands.maximum_target_error(
                    clearance_plan.initial_left_hand_q_rad,
                    clearance_plan.initial_right_hand_q_rad,
                )[2],
                0.0,
            )
            if held_error > dex3_config.posture_position_tolerance_rad:
                raise RuntimeError(
                    "live Dex3 state changed between read-only planning and "
                    f"measured-state hold acquisition by {held_error:.4f}rad; "
                    f"limit is {dex3_config.posture_position_tolerance_rad:.4f}rad"
                )
            driver.start()
            synchronized.acquire(operator_confirmed=True)
            _wait_for_control_state(
                synchronized,
                driver,
                ExecutorState.READY,
                timeout_s=executor_config.motion_timeout_s + 5.0,
                control_maintenance=dex3_controller.maintain_initial_posture,
            )
            synchronized.start_pose(
                RIGHT_CLEARANCE_POSE_ID,
                operator_confirmed=True,
            )
            _wait_for_control_state(
                synchronized,
                driver,
                ExecutorState.READY,
                timeout_s=executor_config.motion_timeout_s + 5.0,
                control_maintenance=dex3_controller.maintain_initial_posture,
            )
            synchronized.start_pose(
                DUAL_CLEARANCE_POSE_ID,
                operator_confirmed=True,
            )
            _wait_for_control_state(
                synchronized,
                driver,
                ExecutorState.READY,
                timeout_s=executor_config.motion_timeout_s + 5.0,
                control_maintenance=dex3_controller.maintain_initial_posture,
            )
            print(
                "ARM CLEARANCE ACTIVE — both shoulders reached the validated "
                "outward position; rechecking the complete finger "
                "sweep at the measured loaded arm state"
            )
            loaded_state = synchronized.observe()
            loaded_hands = _wait_for_dex3_state(dex3_controller.observer, 5.0)
            loaded_sweep = _run_isolated_control_work(
                label="measured loaded-state Dex3 finger-sweep validation",
                worker=_validate_loaded_dex3_finger_sweep_worker,
                worker_kwargs={
                    "urdf_path": str(_configured_gravity_urdf(args.hardware_config)),
                    "collision_config": live_collision,
                    "body_q": loaded_state.position,
                    "initial_left_hand_q_rad": loaded_hands.left.position,
                    "initial_right_hand_q_rad": loaded_hands.right.position,
                    "target_left_hand_q_rad": dex3_config.left_target_q_rad,
                    "target_right_hand_q_rad": dex3_config.right_target_q_rad,
                    "path_config": base_path_config,
                },
                driver=driver,
                control_maintenance=dex3_controller.maintain_initial_posture,
            )
            if not loaded_sweep.passed:
                raise RuntimeError(
                    "measured loaded-state Dex3 finger sweep failed: "
                    f"{loaded_sweep.failure}"
                )
            loaded_pair = loaded_sweep.minimum_pair
            loaded_pair_text = (
                "unknown" if loaded_pair is None else "/".join(loaded_pair)
            )
            loaded_recovery = loaded_sweep.recovered_start_limit_joints
            loaded_recovery_text = (
                "none" if not loaded_recovery else ",".join(loaded_recovery)
            )
            print(
                "MEASURED LOADED-STATE FINGER SWEEP PASSED — minimum clearance="
                f"{loaded_sweep.minimum_clearance_m:.4f}m at "
                f"{loaded_pair_text} across {loaded_sweep.sample_count} samples; "
                f"measured start-limit recovery={loaded_recovery_text}; "
                "beginning the measured-state-limited Dex3 command"
            )
            settled = dex3_controller.acquire_posture(
                safety_heartbeat=driver.check,
            )
            deadline = time.monotonic() + args.duration_s
            while time.monotonic() < deadline:
                dex3_controller.maintain_posture()
                driver.check()
                time.sleep(1.0 / dex3_config.command_rate_hz)
            restored = dex3_controller.restore_initial_posture(
                safety_heartbeat=driver.check,
            )
            synchronized.start_pose(
                RIGHT_CLEARANCE_POSE_ID,
                operator_confirmed=True,
            )
            _wait_for_control_state(
                synchronized,
                driver,
                ExecutorState.READY,
                timeout_s=executor_config.motion_timeout_s + 5.0,
                control_maintenance=dex3_controller.maintain_initial_posture,
            )
            synchronized.start_pose(HANDOFF_POSE_ID, operator_confirmed=True)
            _wait_for_control_state(
                synchronized,
                driver,
                ExecutorState.READY,
                timeout_s=executor_config.motion_timeout_s + 5.0,
                control_maintenance=dex3_controller.maintain_initial_posture,
            )
            synchronized.begin_clean_release(operator_confirmed=True)
            _wait_for_control_state(
                synchronized,
                driver,
                ExecutorState.STOPPED,
                timeout_s=executor_config.release_ramp_s + 5.0,
                control_maintenance=dex3_controller.maintain_initial_posture,
            )
            dex3_controller.timeout()
            dex3_controller.close()
            dex3_controller = None
            driver.close()
            driver.check()
            driver = None
            watchdog.disarm()
            side, motor_index, maximum_error = settled.maximum_target_error(
                dex3_config.left_target_q_rad,
                dex3_config.right_target_q_rad,
            )
            restore_error = max(
                restored.maximum_target_error(
                    clearance_plan.initial_left_hand_q_rad,
                    clearance_plan.initial_right_hand_q_rad,
                )[2],
                0.0,
            )
            print(
                "Dex3 middle-close commissioning passed: both hands reached and "
                "settled at the configured NVIDIA target; worst final target "
                f"error={maximum_error:.6f}rad at {side} motor {motor_index} "
                f"({dex3_motor_joint_name(side, motor_index)}), "
                "maximum final velocity="
                f"{settled.maximum_abs_velocity_rad_s:.6f}rad/s; restored initial "
                f"finger posture with worst error={restore_error:.6f}rad; reversed "
                "the validated shoulder route; terminal hand timeout and arm_sdk "
                "weight zero completed"
            )
            return 0
        except BaseException as error:
            primary_error = error
            local_timeout_error = None
            if dex3_controller is not None:
                try:
                    dex3_controller.timeout()
                except BaseException as error:  # noqa: BLE001 - PC2 is backup.
                    local_timeout_error = error
            if driver is not None:
                _attempt_safety_cleanup(
                    cleanup_errors,
                    "clearance control driver stop",
                    driver.close,
                )
            if watchdog is not None and watchdog.armed:
                try:
                    watchdog.damp(
                        "Dex3 middle-close commissioning failed or was interrupted"
                    )
                    if synchronized is not None:
                        synchronized.confirm_external_damping(
                            "PC2 verified whole-body damping after commissioning fault"
                        )
                except BaseException as cleanup_error:  # noqa: BLE001
                    cleanup_errors.append(("PC2 damping", cleanup_error))
            if local_timeout_error is not None and (
                watchdog is None or watchdog.terminal_action is None
            ):
                cleanup_errors.append(("local Dex3 timeout", local_timeout_error))
            _raise_safety_cleanup_failures(primary_error, cleanup_errors)
            raise
        finally:
            if driver is not None:
                _attempt_safety_cleanup(
                    cleanup_errors,
                    "clearance control driver close",
                    driver.close,
                )
            if dex3_controller is not None:
                if (
                    not dex3_controller.timed_out
                    and watchdog is not None
                    and (watchdog.terminal_action is not None)
                ):
                    dex3_controller.close_after_external_timeout()
                elif dex3_controller.timed_out or dex3_controller.command_count == 0:
                    dex3_controller.close()
            if dex3_observer is not None:
                dex3_observer.close()
            if transport is not None and transport.command_count == 0:
                transport.close()
            if lowstate is not None:
                lowstate.close()
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
